aahnguye101024/LEDArtBoard/LEDBoard/LEDBoard/LEDBoard.sch

## KiCad design LEDBoard/LEDBoard/LEDBoard.sch (2024-01-31)

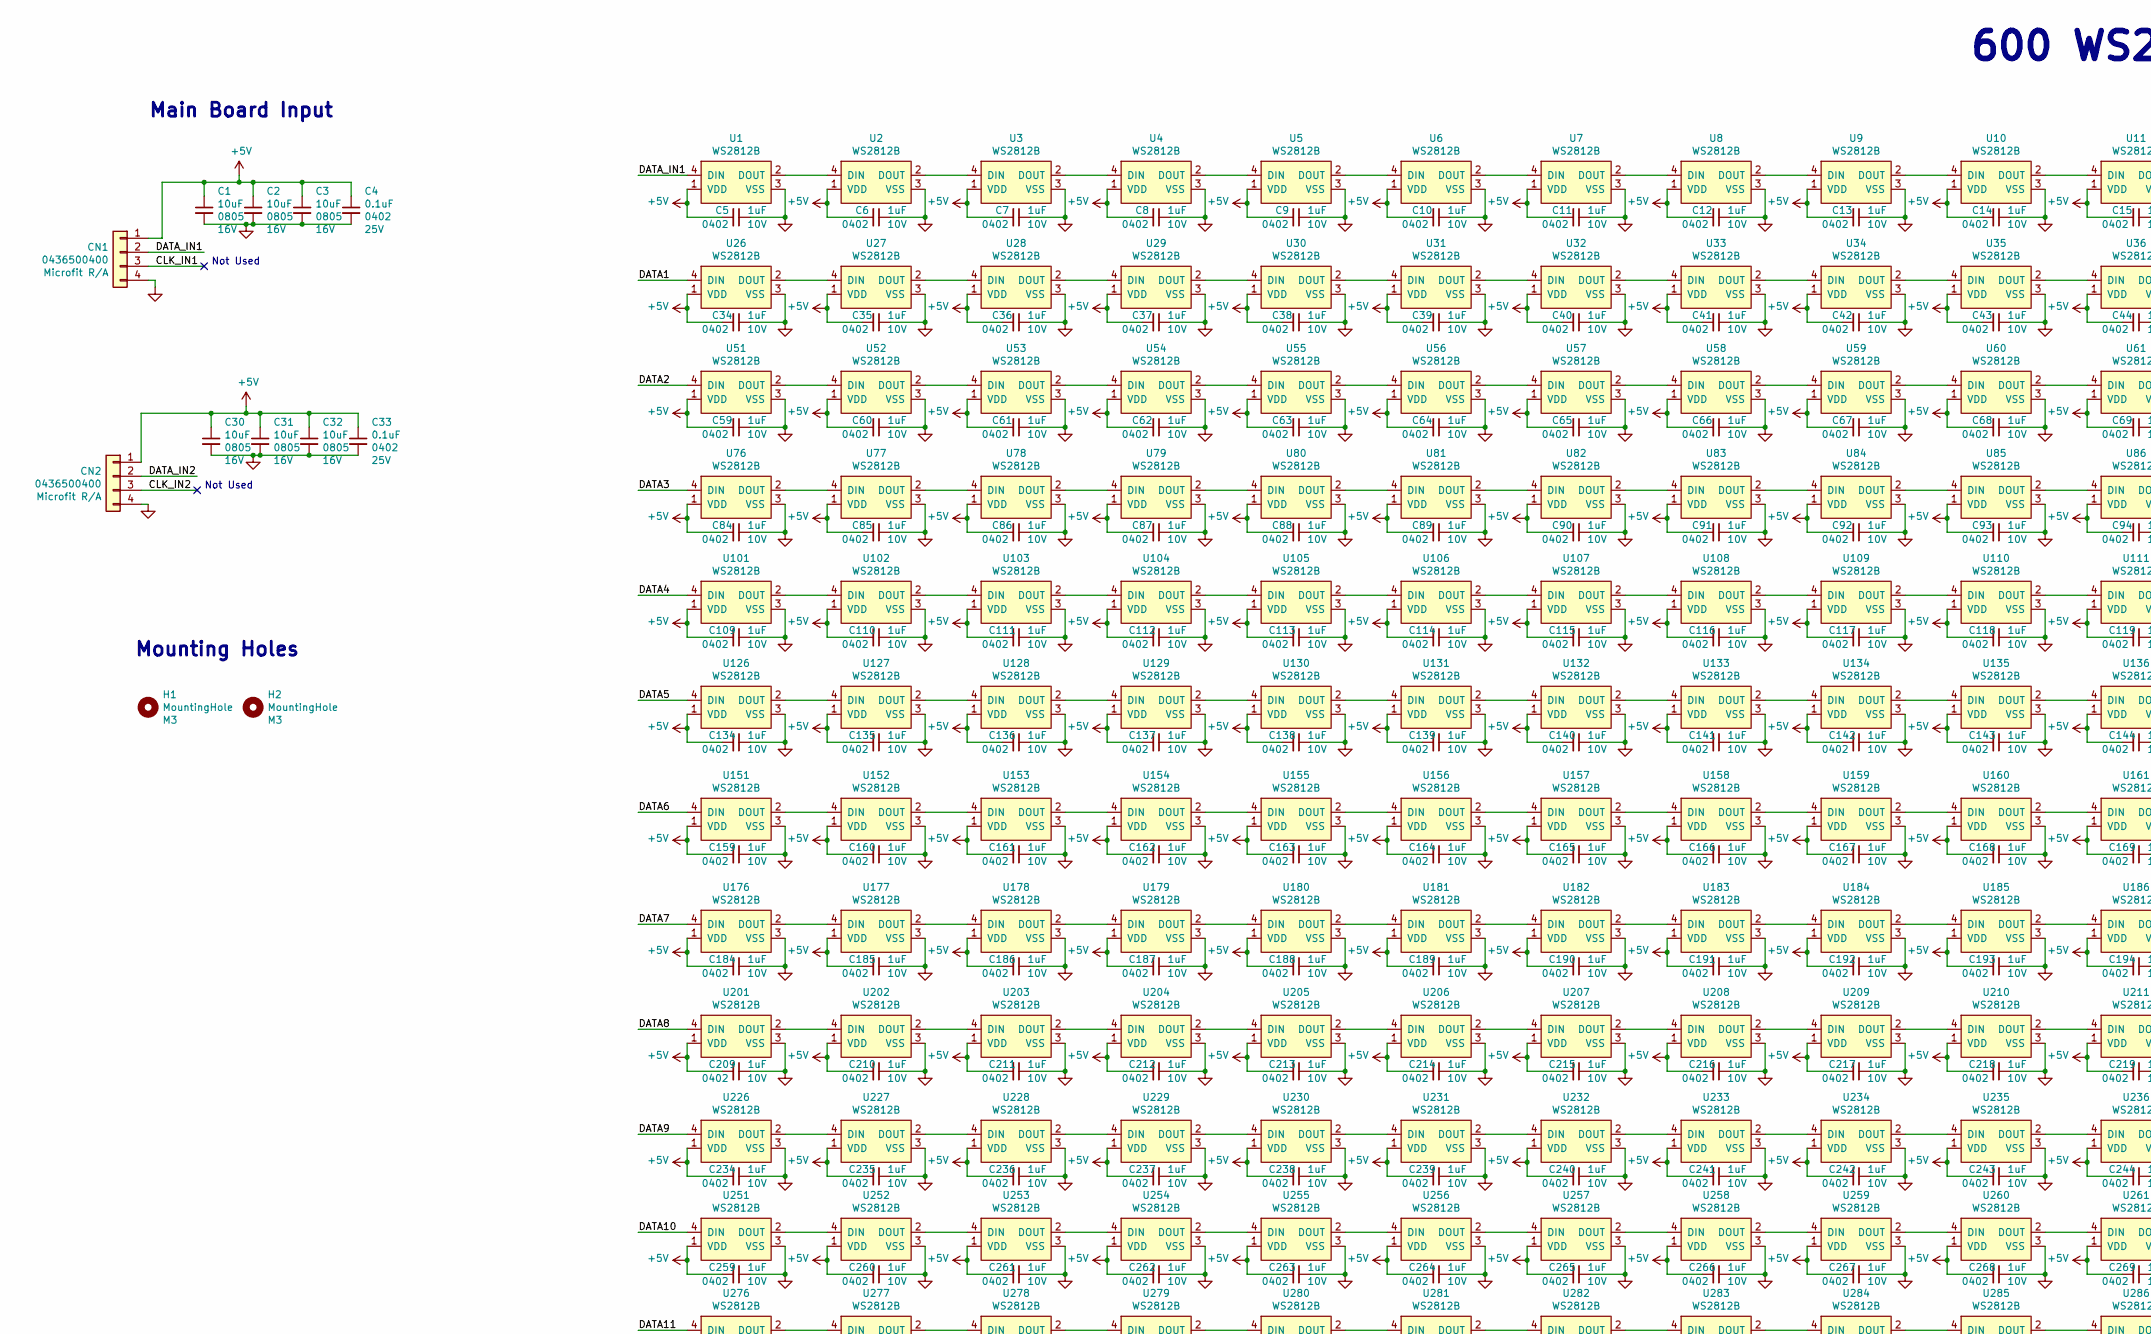
[picture p12: schematic LEDBoard.sch, part in row 1, column 1]

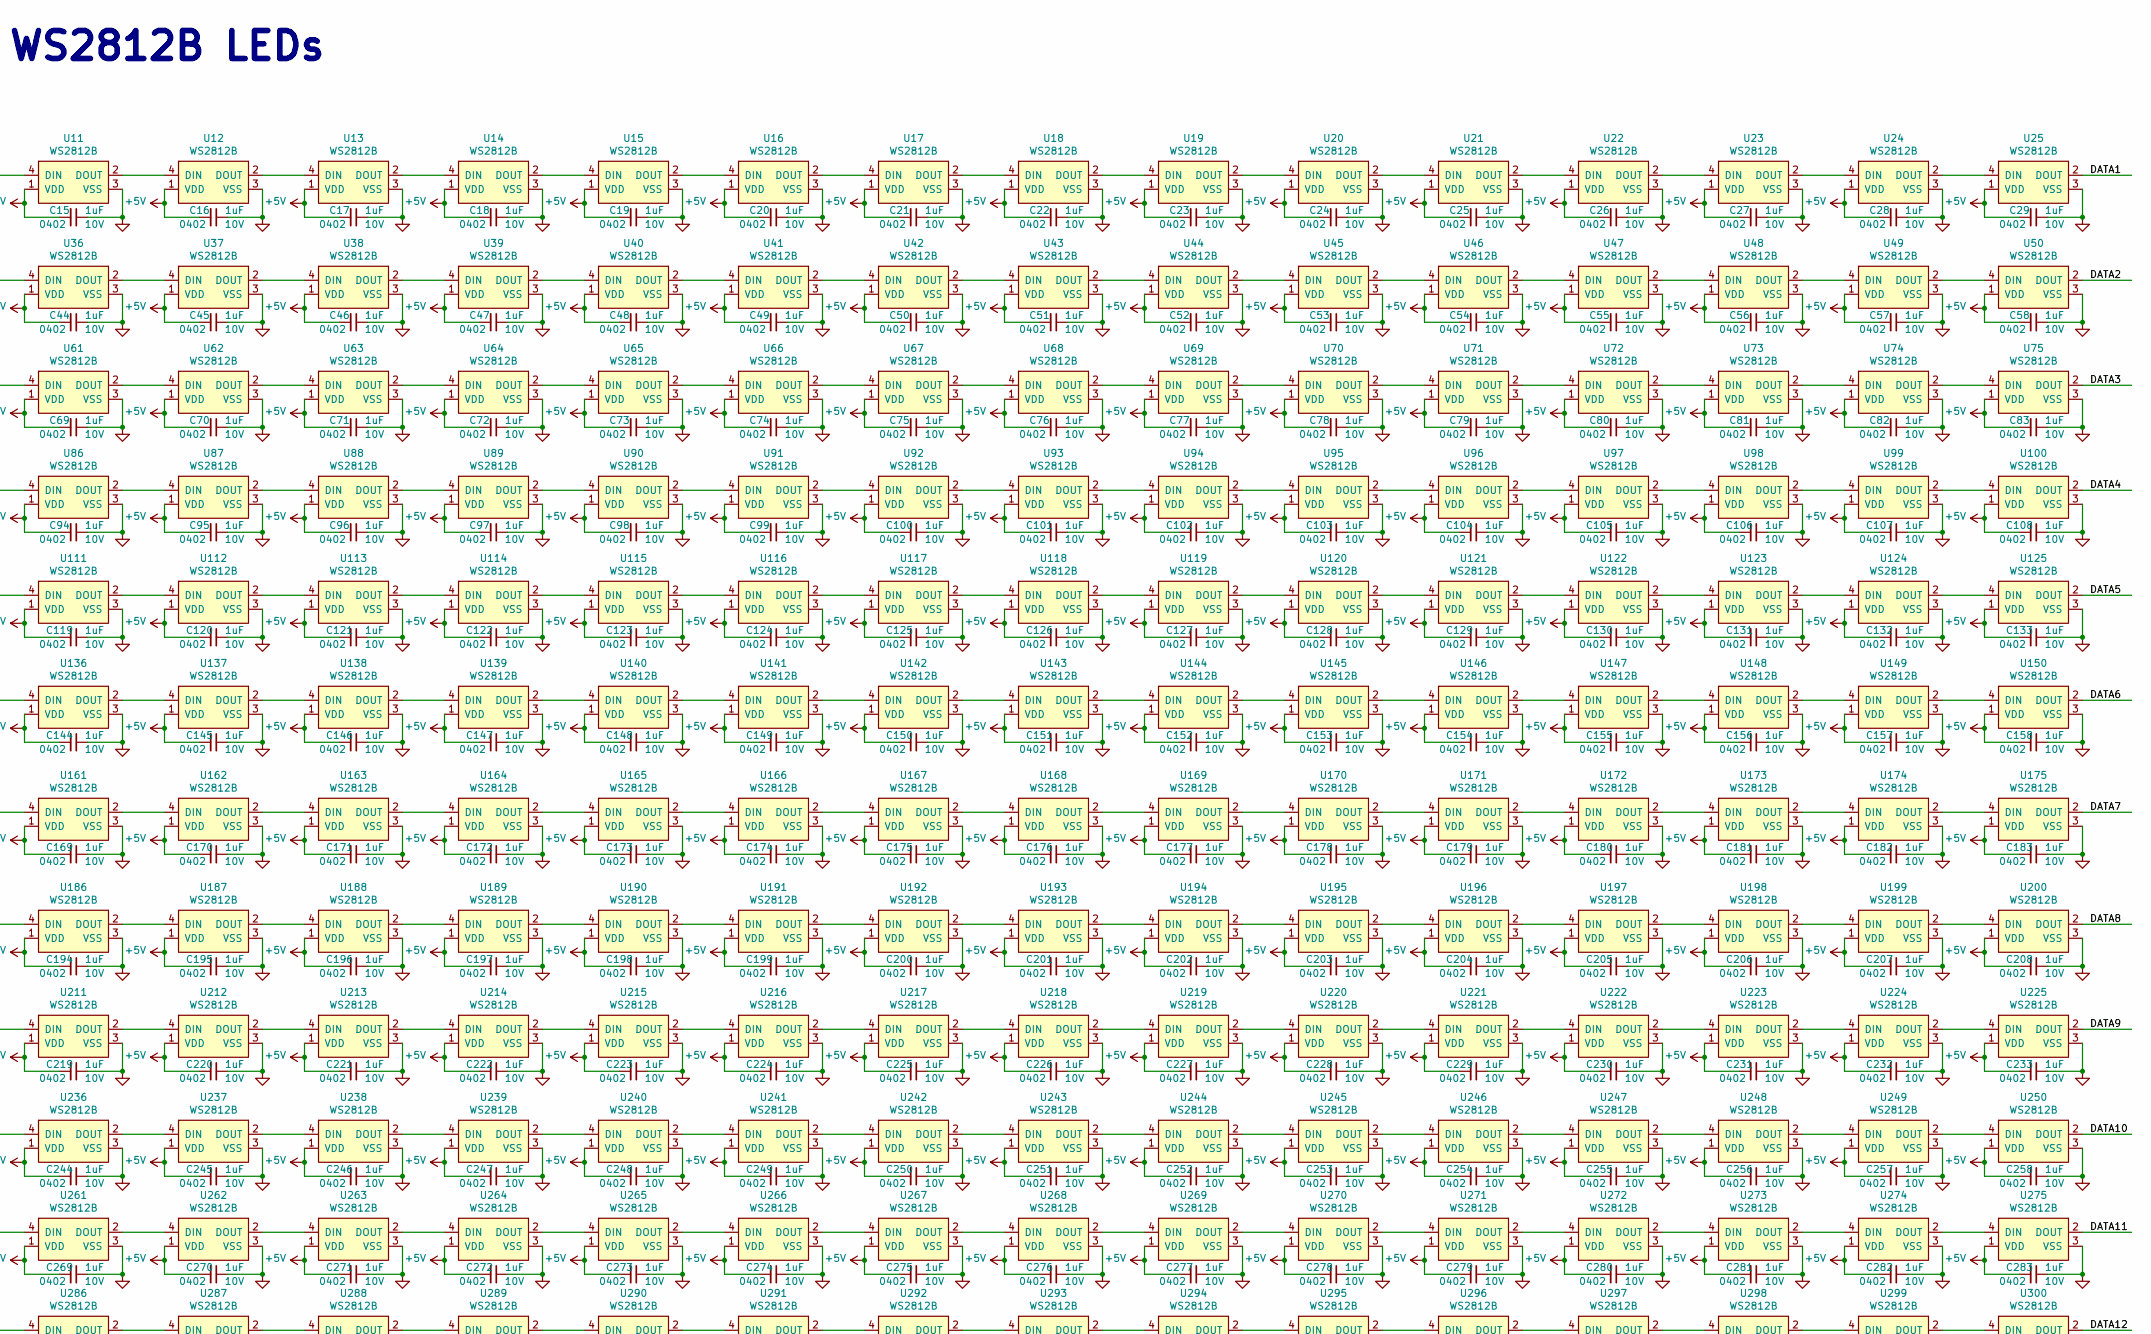
[picture p13: schematic LEDBoard.sch, part in row 1, column 2]

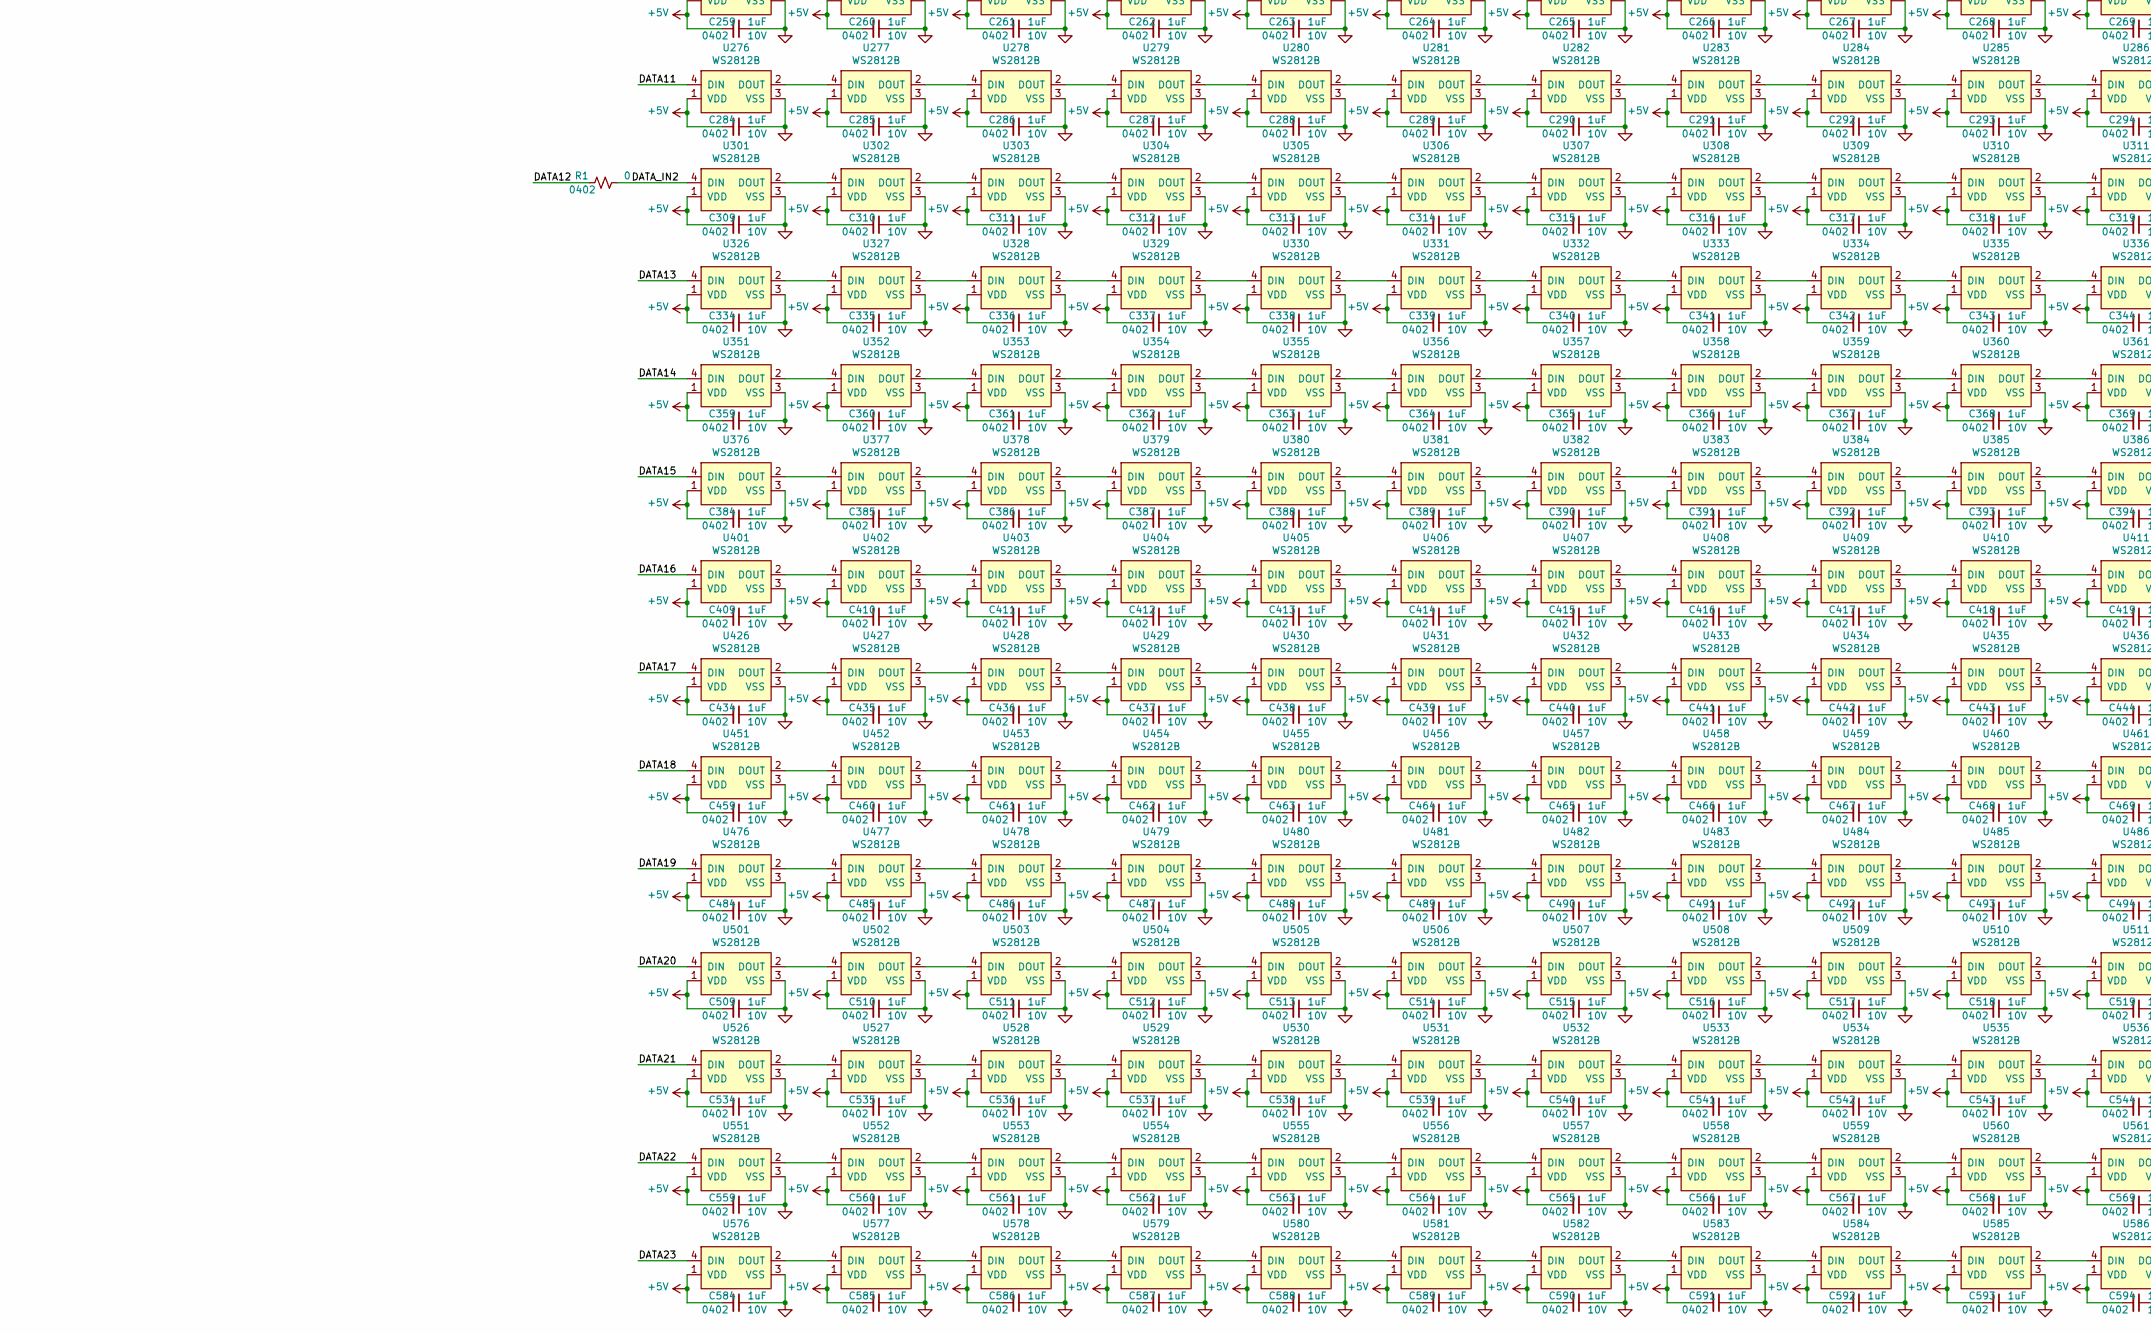
[picture p14: schematic LEDBoard.sch, part in row 2, column 1]

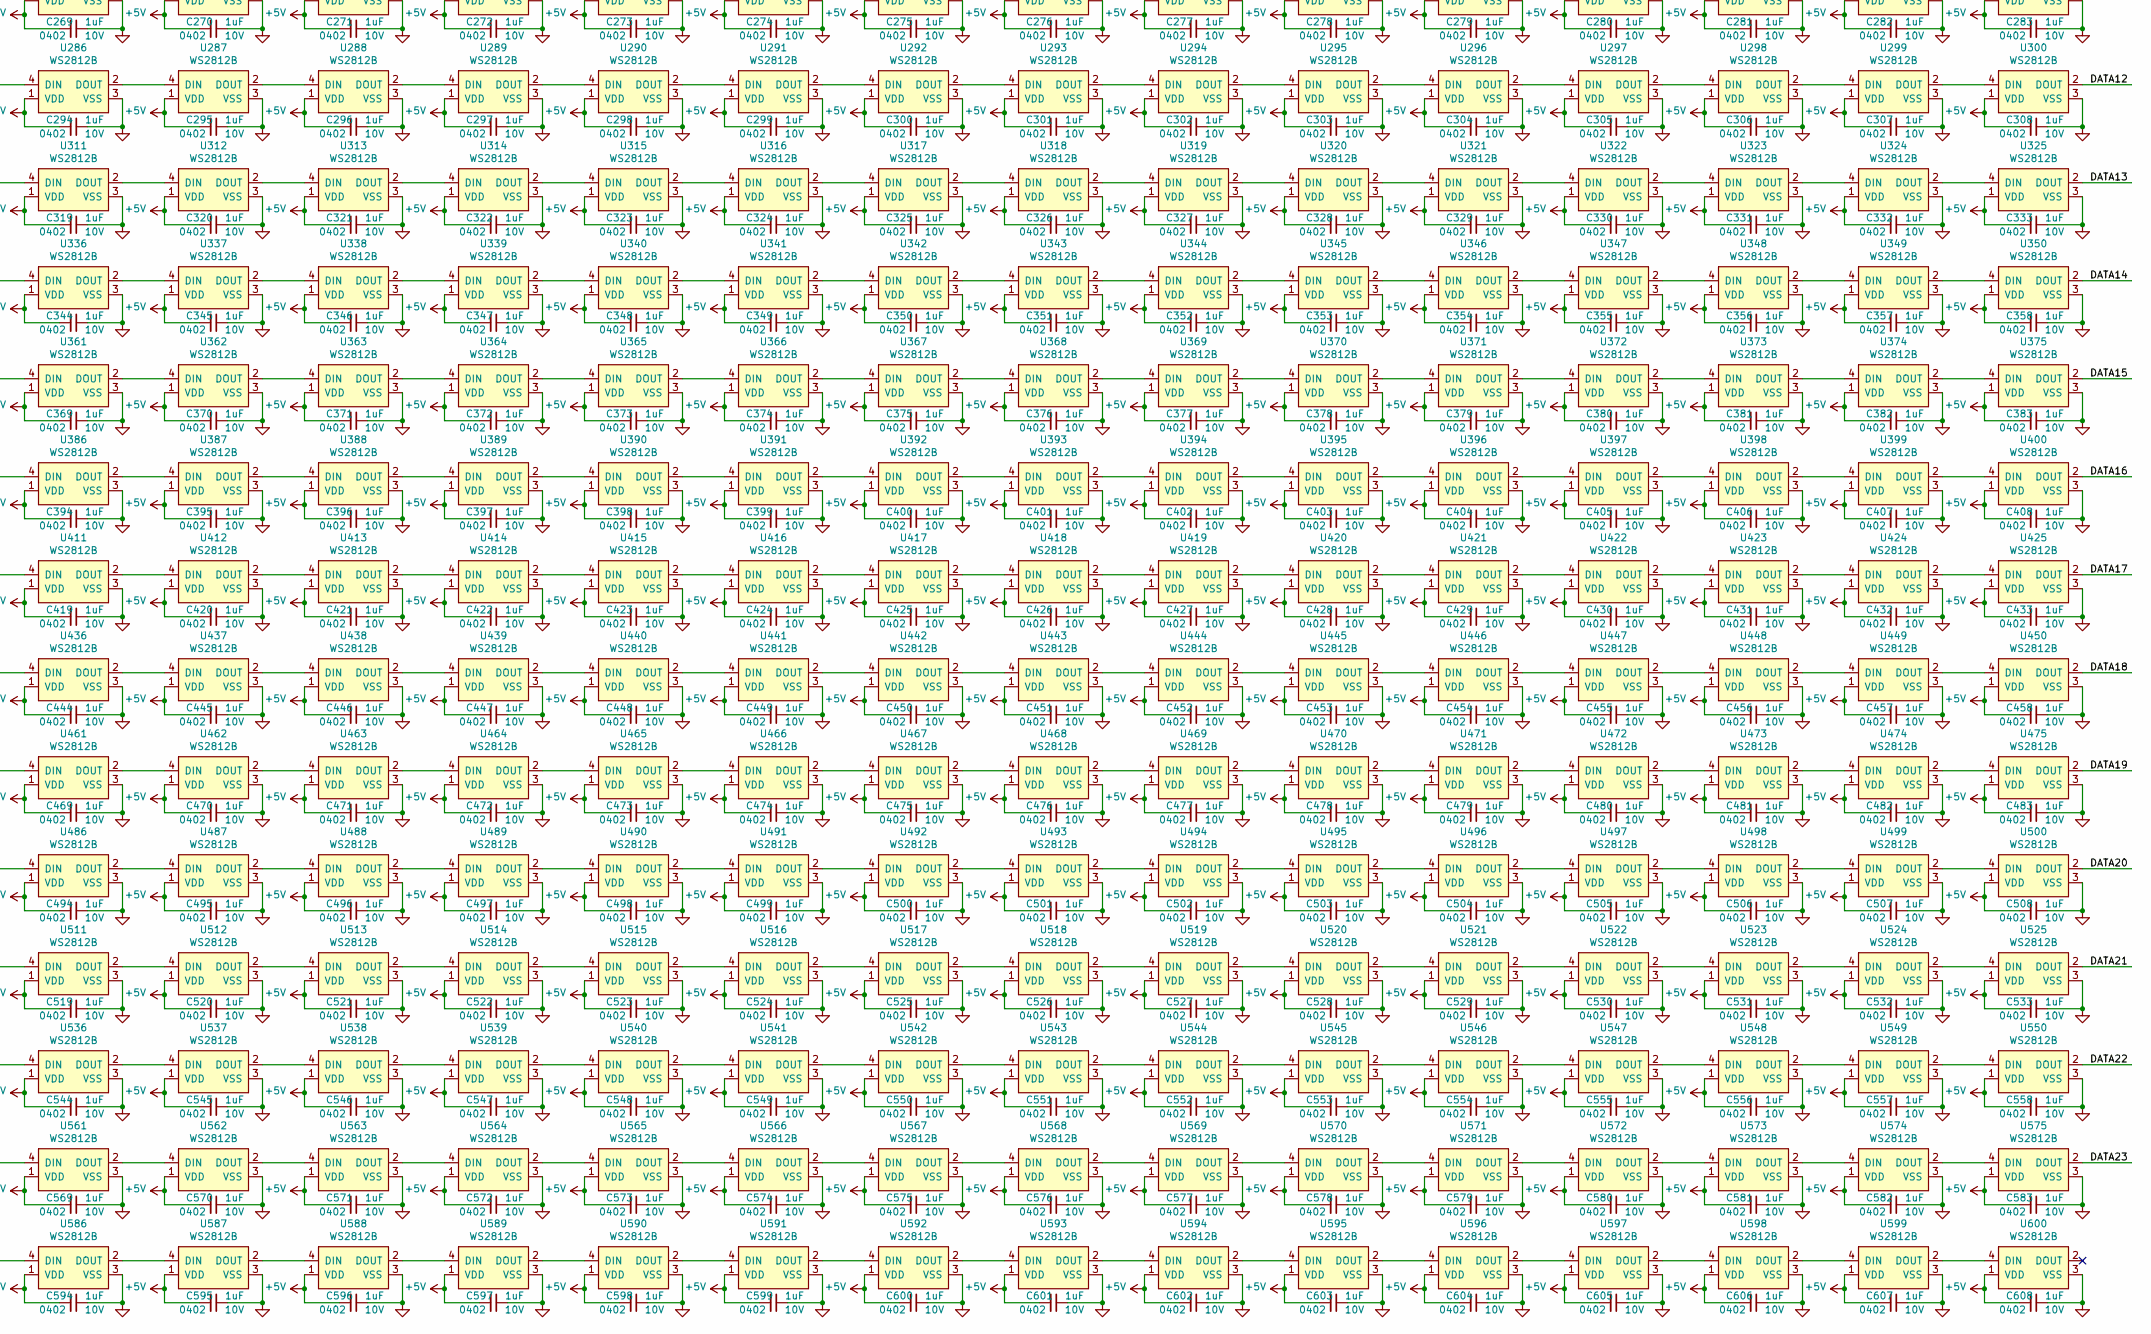
[picture p15: schematic LEDBoard.sch, part in row 2, column 2]

Parts:
C1, C2, C3, C30, C31, C32: 10uF; C_0805_2012Metric; Voltage 16V; Part Number 1276-2893-1-ND
C4, C33: 0.1uF; C_0402_1005Metric; Voltage 25V; Part Number 1276-1043-1-ND
C5, C6, C7, C8, C9, C10, C11, C12, C13, C14, C15, C16, C17, C18, C19, C20, C21, C22, C23, C24, C25, C26, C27, C28, C29, C34, C35, C36, C37, C38, C39, C40, C41, C42, C43, C44, C45, C46, C47, C48, C49, C50, C51, C52, C53, C54, C55, C56, C57, C58, C59, C60, C61, C62, C63, C64, C65, C66, C67, C68, C69, C70, C71, C72, C73, C74, C75, C76, C77, C78, C79, C80, C81, C82, C83, C84, C85, C86, C87, C88, C89, C90, C91, C92, C93, C94, C95, C96, C97, C98, C99, C100, C101, C102, C103, C104, C105, C106, C107, C108, C109, C110, C111, C112, C113, C114, C115, C116, C117, C118, C119, C120, C121, C122, C123, C124, C125, C126, C127, C128, C129, C130, C131, C132, C133, C134, C135, C136, C137, C138, C139, C140, C141, C142, C143, C144, C145, C146, C147, C148, C149, C150, C151, C152, C153, C154, C155, C156, C157, C158, C159, C160, C161, C162, C163, C164, C165, C166, C167, C168, C169, C170, C171, C172, C173, C174, C175, C176, C177, C178, C179, C180, C181, C182, C183, C184, C185, C186, C187, C188, C189, C190, C191, C192, C193, C194, C195, C196, C197, C198, C199, C200, C201, C202, C203, C204, C205, C206, C207, C208, C209, C210, C211, C212, C213, C214, C215, C216, C217, C218, C219, C220, C221, C222, C223, C224, C225, C226, C227, C228, C229, C230, C231, C232, C233, C234, C235, C236, C237, C238, C239, C240, C241, C242, C243, C244, C245, C246, C247, C248, C249, C250, C251, C252, C253, C254, C255, C256, C257, C258, C259, C260, C261, C262, C263, C264, C265, C266, C267, C268, C269, C270, C271, C272, C273, C274, C275, C276, C277, C278, C279, C280, C281, C282, C283, C284, C285, C286, C287, C288, C289, C290, C291, C292, C293, C294, C295, C296, C297, C298, C299, C300, C301, C302, C303, C304, C305, C306, C307, C308, C309, C310, C311, C312, C313, C314, C315, C316, C317, C318, C319, C320, C321, C322, C323, C324, C325, C326, C327, C328, C329, C330, C331, C332, C333, C334, C335, C336, C337, C338, C339, C340, C341, C342, C343, C344, C345, C346, C347, C348, C349, C350, C351, C352, C353, C354, C355, C356, C357, C358, C359, C360, C361, C362, C363, C364, C365, C366, C367, C368, C369, C370, C371, C372, C373, C374, C375, C376, C377, C378, C379, C380, C381, C382, C383, C384, C385, C386, C387, C388, C389, C390, C391, C392, C393, C394, C395, C396, C397, C398, C399, C400, C401, C402, C403, C404, C405, C406, C407, C408, C409, C410, C411, C412, C413, C414, C415, C416, C417, C418, C419, C420, C421, C422, C423, C424, C425, C426, C427, C428, C429, C430, C431, C432, C433, C434, C435, C436, C437, C438, C439, C440, C441, C442, C443, C444, C445, C446, C447, C448, C449, C450, C451, C452, C453, C454, C455, C456, C457, C458, C459, C460, C461, C462, C463, C464, C465, C466, C467, C468, C469, C470, C471, C472, C473, C474, C475, C476, C477, C478, C479, C480, C481, C482, C483, C484, C485, C486, C487, C488, C489, C490, C491, C492, C493, C494, C495, C496, C497, C498, C499, C500, C501, C502, C503, C504, C505, C506, C507, C508, C509, C510, C511, C512, C513, C514, C515, C516, C517, C518, C519, C520, C521, C522, C523, C524, C525, C526, C527, C528, C529, C530, C531, C532, C533, C534, C535, C536, C537, C538, C539, C540, C541, C542, C543, C544, C545, C546, C547, C548, C549, C550, C551, C552, C553, C554, C555, C556, C557, C558, C559, C560, C561, C562, C563, C564, C565, C566, C567, C568, C569, C570, C571, C572, C573, C574, C575, C576, C577, C578, C579, C580, C581, C582, C583, C584, C585, C586, C587, C588, C589, C590, C591, C592, C593, C594, C595, C596, C597, C598, C599, C600, C601, C602, C603, C604, C605, C606, C607, C608: 1uF; C_0402_1005Metric; Voltage 10V; Part Number 1276-1076-1-ND
CN1, CN2: 0436500400; MOLEX_43650-0400; Part Number WM1862-ND
H1, H2: MountingHole; MountingHole_3.2mm_M3_ISO7380
R1: 0; R_0402_1005Metric; Part Number RMCF0402ZT0R00CT-ND
U1, U2, U3, U4, U5, U6, U7, U8, U9, U10, U11, U12, U13, U14, U15, U16, U17, U18, U19, U20, U21, U22, U23, U24, U25, U26, U27, U28, U29, U30, U31, U32, U33, U34, U35, U36, U37, U38, U39, U40, U41, U42, U43, U44, U45, U46, U47, U48, U49, U50, U51, U52, U53, U54, U55, U56, U57, U58, U59, U60, U61, U62, U63, U64, U65, U66, U67, U68, U69, U70, U71, U72, U73, U74, U75, U76, U77, U78, U79, U80, U81, U82, U83, U84, U85, U86, U87, U88, U89, U90, U91, U92, U93, U94, U95, U96, U97, U98, U99, U100, U101, U102, U103, U104, U105, U106, U107, U108, U109, U110, U111, U112, U113, U114, U115, U116, U117, U118, U119, U120, U121, U122, U123, U124, U125, U126, U127, U128, U129, U130, U131, U132, U133, U134, U135, U136, U137, U138, U139, U140, U141, U142, U143, U144, U145, U146, U147, U148, U149, U150, U151, U152, U153, U154, U155, U156, U157, U158, U159, U160, U161, U162, U163, U164, U165, U166, U167, U168, U169, U170, U171, U172, U173, U174, U175, U176, U177, U178, U179, U180, U181, U182, U183, U184, U185, U186, U187, U188, U189, U190, U191, U192, U193, U194, U195, U196, U197, U198, U199, U200, U201, U202, U203, U204, U205, U206, U207, U208, U209, U210, U211, U212, U213, U214, U215, U216, U217, U218, U219, U220, U221, U222, U223, U224, U225, U226, U227, U228, U229, U230, U231, U232, U233, U234, U235, U236, U237, U238, U239, U240, U241, U242, U243, U244, U245, U246, U247, U248, U249, U250, U251, U252, U253, U254, U255, U256, U257, U258, U259, U260, U261, U262, U263, U264, U265, U266, U267, U268, U269, U270, U271, U272, U273, U274, U275, U276, U277, U278, U279, U280, U281, U282, U283, U284, U285, U286, U287, U288, U289, U290, U291, U292, U293, U294, U295, U296, U297, U298, U299, U300, U301, U302, U303, U304, U305, U306, U307, U308, U309, U310, U311, U312, U313, U314, U315, U316, U317, U318, U319, U320, U321, U322, U323, U324, U325, U326, U327, U328, U329, U330, U331, U332, U333, U334, U335, U336, U337, U338, U339, U340, U341, U342, U343, U344, U345, U346, U347, U348, U349, U350, U351, U352, U353, U354, U355, U356, U357, U358, U359, U360, U361, U362, U363, U364, U365, U366, U367, U368, U369, U370, U371, U372, U373, U374, U375, U376, U377, U378, U379, U380, U381, U382, U383, U384, U385, U386, U387, U388, U389, U390, U391, U392, U393, U394, U395, U396, U397, U398, U399, U400, U401, U402, U403, U404, U405, U406, U407, U408, U409, U410, U411, U412, U413, U414, U415, U416, U417, U418, U419, U420, U421, U422, U423, U424, U425, U426, U427, U428, U429, U430, U431, U432, U433, U434, U435, U436, U437, U438, U439, U440, U441, U442, U443, U444, U445, U446, U447, U448, U449, U450, U451, U452, U453, U454, U455, U456, U457, U458, U459, U460, U461, U462, U463, U464, U465, U466, U467, U468, U469, U470, U471, U472, U473, U474, U475, U476, U477, U478, U479, U480, U481, U482, U483, U484, U485, U486, U487, U488, U489, U490, U491, U492, U493, U494, U495, U496, U497, U498, U499, U500, U501, U502, U503, U504, U505, U506, U507, U508, U509, U510, U511, U512, U513, U514, U515, U516, U517, U518, U519, U520, U521, U522, U523, U524, U525, U526, U527, U528, U529, U530, U531, U532, U533, U534, U535, U536, U537, U538, U539, U540, U541, U542, U543, U544, U545, U546, U547, U548, U549, U550, U551, U552, U553, U554, U555, U556, U557, U558, U559, U560, U561, U562, U563, U564, U565, U566, U567, U568, U569, U570, U571, U572, U573, U574, U575, U576, U577, U578, U579, U580, U581, U582, U583, U584, U585, U586, U587, U588, U589, U590, U591, U592, U593, U594, U595, U596, U597, U598, U599, U600: WS2812B; LED_WS2812B-B; Part Number C2761795; JLCPCB Part Number C2761795

Connections:
+5V: C1.1, C2.1, C3.1, C4.1, C5.2, C6.2, C7.2, C8.2, C9.2, C10.2, C11.2, C12.2, C13.2, C14.2, C15.2, C16.2, C17.2, C18.2, C19.2, C20.2, C21.2, C22.2, C23.2, C24.2, C25.2, C26.2, C27.2, C28.2, C29.2, C30.1, C31.1, C32.1, C33.1, C34.2, C35.2, C36.2, C37.2, C38.2, C39.2, C40.2, C41.2, C42.2, C43.2, C44.2, C45.2, C46.2, C47.2, C48.2, C49.2, C50.2, C51.2, C52.2, C53.2, C54.2, C55.2, C56.2, C57.2, C58.2, C59.2, C60.2, C61.2, C62.2, C63.2, C64.2, C65.2, C66.2, C67.2, C68.2, C69.2, C70.2, C71.2, C72.2, C73.2, C74.2, C75.2, C76.2, C77.2, C78.2, C79.2, C80.2, C81.2, C82.2, C83.2, C84.2, C85.2, C86.2, C87.2, C88.2, C89.2, C90.2, C91.2, C92.2, C93.2, C94.2, C95.2, C96.2, C97.2, C98.2, C99.2, C100.2, C101.2, C102.2, C103.2, C104.2, C105.2, C106.2, C107.2, C108.2, C109.2, C110.2, C111.2, C112.2, C113.2, C114.2, C115.2, C116.2, C117.2, C118.2, C119.2, C120.2, C121.2, C122.2, C123.2, C124.2, C125.2, C126.2, C127.2, C128.2, C129.2, C130.2, C131.2, C132.2, C133.2, C134.2, C135.2, C136.2, C137.2, C138.2, C139.2, C140.2, C141.2, C142.2, C143.2, C144.2, C145.2, C146.2, C147.2, C148.2, C149.2, C150.2, C151.2, C152.2, C153.2, C154.2, C155.2, C156.2, C157.2, C158.2, C159.2, C160.2, C161.2, C162.2, C163.2, C164.2, C165.2, C166.2, C167.2, C168.2, C169.2, C170.2, C171.2, C172.2, C173.2, C174.2, C175.2, C176.2, C177.2, C178.2, C179.2, C180.2, C181.2, C182.2, C183.2, C184.2, C185.2, C186.2, C187.2, C188.2, C189.2, C190.2, C191.2, C192.2, C193.2, C194.2, C195.2, C196.2, C197.2, C198.2, C199.2, C200.2, C201.2, C202.2, C203.2, C204.2, C205.2, C206.2, C207.2, C208.2, C209.2, C210.2, C211.2, C212.2, C213.2, C214.2, C215.2, C216.2, C217.2, C218.2, C219.2, C220.2, C221.2, C222.2, C223.2, C224.2, C225.2, C226.2, C227.2, C228.2, C229.2, C230.2, C231.2, C232.2, C233.2, C234.2, C235.2, C236.2, C237.2, C238.2, C239.2, C240.2, C241.2, C242.2, C243.2, C244.2, C245.2, C246.2, C247.2, C248.2, C249.2, C250.2, C251.2, C252.2, C253.2, C254.2, C255.2, C256.2, C257.2, C258.2, C259.2, C260.2, C261.2, C262.2, C263.2, C264.2, C265.2, C266.2, C267.2, C268.2, C269.2, C270.2, C271.2, C272.2, C273.2, C274.2, C275.2, C276.2, C277.2, C278.2, C279.2, C280.2, C281.2, C282.2, C283.2, C284.2, C285.2, C286.2, C287.2, C288.2, C289.2, C290.2, C291.2, C292.2, C293.2, C294.2, C295.2, C296.2, C297.2, C298.2, C299.2, C300.2, C301.2, C302.2, C303.2, C304.2, C305.2, C306.2, C307.2, C308.2, C309.2, C310.2, C311.2, C312.2, C313.2, C314.2, C315.2, C316.2, C317.2, C318.2, C319.2, C320.2, C321.2, C322.2, C323.2, C324.2, C325.2, C326.2, C327.2, C328.2, C329.2, C330.2, C331.2, C332.2, C333.2, C334.2, C335.2, C336.2, C337.2, C338.2, C339.2, C340.2, C341.2, C342.2, C343.2, C344.2, C345.2, C346.2, C347.2, C348.2, C349.2, C350.2, C351.2, C352.2, C353.2, C354.2, C355.2, C356.2, C357.2, C358.2, C359.2, C360.2, C361.2, C362.2, C363.2, C364.2, C365.2, C366.2, C367.2, C368.2, C369.2, C370.2, C371.2, C372.2, C373.2, C374.2, C375.2, C376.2, C377.2, C378.2, C379.2, C380.2, C381.2, C382.2, C383.2, C384.2, C385.2, C386.2, C387.2, C388.2, C389.2, C390.2, C391.2, C392.2, C393.2, C394.2, C395.2, C396.2, C397.2, C398.2, C399.2, C400.2, C401.2, C402.2, C403.2, C404.2, C405.2, C406.2, C407.2, C408.2, C409.2, C410.2, C411.2, C412.2, C413.2, C414.2, C415.2, C416.2, C417.2, C418.2, C419.2, C420.2, C421.2, C422.2, C423.2, C424.2, C425.2, C426.2, C427.2, C428.2, C429.2, C430.2, C431.2, C432.2, C433.2, C434.2, C435.2, C436.2, C437.2, C438.2, C439.2, C440.2, C441.2, C442.2, C443.2, C444.2, C445.2, C446.2, C447.2, C448.2, C449.2, C450.2, C451.2, C452.2, C453.2, C454.2, C455.2, C456.2, C457.2, C458.2, C459.2, C460.2, C461.2, C462.2, C463.2, C464.2, C465.2, C466.2, C467.2, C468.2, C469.2, C470.2, C471.2, C472.2, C473.2, C474.2, C475.2, C476.2, C477.2, C478.2, C479.2, C480.2, C481.2, C482.2, C483.2, C484.2, C485.2, C486.2, C487.2, C488.2, C489.2, C490.2, C491.2, C492.2, C493.2, C494.2, C495.2, C496.2, C497.2, C498.2, C499.2, C500.2, C501.2, C502.2, C503.2, C504.2, C505.2, C506.2, C507.2, C508.2, C509.2, C510.2, C511.2, C512.2, C513.2, C514.2, C515.2, C516.2, C517.2, C518.2, C519.2, C520.2, C521.2, C522.2, C523.2, C524.2, C525.2, C526.2, C527.2, C528.2, C529.2, C530.2, C531.2, C532.2, C533.2, C534.2, C535.2, C536.2, C537.2, C538.2, C539.2, C540.2, C541.2, C542.2, C543.2, C544.2, C545.2, C546.2, C547.2, C548.2, C549.2, C550.2, C551.2, C552.2, C553.2, C554.2, C555.2, C556.2, C557.2, C558.2, C559.2, C560.2, C561.2, C562.2, C563.2, C564.2, C565.2, C566.2, C567.2, C568.2, C569.2, C570.2, C571.2, C572.2, C573.2, C574.2, C575.2, C576.2, C577.2, C578.2, C579.2, C580.2, C581.2, C582.2, C583.2, C584.2, C585.2, C586.2, C587.2, C588.2, C589.2, C590.2, C591.2, C592.2, C593.2, C594.2, C595.2, C596.2, C597.2, C598.2, C599.2, C600.2, C601.2, C602.2, C603.2, C604.2, C605.2, C606.2, C607.2, C608.2, CN1.1, CN2.1, U1.1 (VDD), U2.1 (VDD), U3.1 (VDD), U4.1 (VDD), U5.1 (VDD), U6.1 (VDD), U7.1 (VDD), U8.1 (VDD), U9.1 (VDD), U10.1 (VDD), U11.1 (VDD), U12.1 (VDD), U13.1 (VDD), U14.1 (VDD), U15.1 (VDD), U16.1 (VDD), U17.1 (VDD), U18.1 (VDD), U19.1 (VDD), U20.1 (VDD), U21.1 (VDD), U22.1 (VDD), U23.1 (VDD), U24.1 (VDD), U25.1 (VDD), U26.1 (VDD), U27.1 (VDD), U28.1 (VDD), U29.1 (VDD), U30.1 (VDD), U31.1 (VDD), U32.1 (VDD), U33.1 (VDD), U34.1 (VDD), U35.1 (VDD), U36.1 (VDD), U37.1 (VDD), U38.1 (VDD), U39.1 (VDD), U40.1 (VDD), U41.1 (VDD), U42.1 (VDD), U43.1 (VDD), U44.1 (VDD), U45.1 (VDD), U46.1 (VDD), U47.1 (VDD), U48.1 (VDD), U49.1 (VDD), U50.1 (VDD), U51.1 (VDD), U52.1 (VDD), U53.1 (VDD), U54.1 (VDD), U55.1 (VDD), U56.1 (VDD), U57.1 (VDD), U58.1 (VDD), U59.1 (VDD), U60.1 (VDD), U61.1 (VDD), U62.1 (VDD), U63.1 (VDD), U64.1 (VDD), U65.1 (VDD), U66.1 (VDD), U67.1 (VDD), U68.1 (VDD), U69.1 (VDD), U70.1 (VDD), U71.1 (VDD), U72.1 (VDD), U73.1 (VDD), U74.1 (VDD), U75.1 (VDD), U76.1 (VDD), U77.1 (VDD), U78.1 (VDD), U79.1 (VDD), U80.1 (VDD), U81.1 (VDD), U82.1 (VDD), U83.1 (VDD), U84.1 (VDD), U85.1 (VDD), U86.1 (VDD), U87.1 (VDD), U88.1 (VDD), U89.1 (VDD), U90.1 (VDD), U91.1 (VDD), U92.1 (VDD), U93.1 (VDD), U94.1 (VDD), U95.1 (VDD), U96.1 (VDD), U97.1 (VDD), U98.1 (VDD), U99.1 (VDD), U100.1 (VDD), U101.1 (VDD), U102.1 (VDD), U103.1 (VDD), U104.1 (VDD), U105.1 (VDD), U106.1 (VDD), U107.1 (VDD), U108.1 (VDD), U109.1 (VDD), U110.1 (VDD), U111.1 (VDD), U112.1 (VDD), U113.1 (VDD), U114.1 (VDD), U115.1 (VDD), U116.1 (VDD), U117.1 (VDD), U118.1 (VDD), U119.1 (VDD), U120.1 (VDD), U121.1 (VDD), U122.1 (VDD), U123.1 (VDD), U124.1 (VDD), U125.1 (VDD), U126.1 (VDD), U127.1 (VDD), U128.1 (VDD), U129.1 (VDD), U130.1 (VDD), U131.1 (VDD), U132.1 (VDD), U133.1 (VDD), U134.1 (VDD), U135.1 (VDD), U136.1 (VDD), U137.1 (VDD), U138.1 (VDD), U139.1 (VDD), U140.1 (VDD), U141.1 (VDD), U142.1 (VDD), U143.1 (VDD), U144.1 (VDD), U145.1 (VDD), U146.1 (VDD), U147.1 (VDD), U148.1 (VDD), U149.1 (VDD), U150.1 (VDD), U151.1 (VDD), U152.1 (VDD), U153.1 (VDD), U154.1 (VDD), U155.1 (VDD), U156.1 (VDD), U157.1 (VDD), U158.1 (VDD), U159.1 (VDD), U160.1 (VDD), U161.1 (VDD), U162.1 (VDD), U163.1 (VDD), U164.1 (VDD), U165.1 (VDD), U166.1 (VDD), U167.1 (VDD), U168.1 (VDD), U169.1 (VDD), U170.1 (VDD), U171.1 (VDD), U172.1 (VDD), U173.1 (VDD), U174.1 (VDD), U175.1 (VDD), U176.1 (VDD), U177.1 (VDD), U178.1 (VDD), U179.1 (VDD), U180.1 (VDD), U181.1 (VDD), U182.1 (VDD), U183.1 (VDD), U184.1 (VDD), U185.1 (VDD), U186.1 (VDD), U187.1 (VDD), U188.1 (VDD), U189.1 (VDD), U190.1 (VDD), U191.1 (VDD), U192.1 (VDD), U193.1 (VDD), U194.1 (VDD), U195.1 (VDD), U196.1 (VDD), U197.1 (VDD), U198.1 (VDD), U199.1 (VDD), U200.1 (VDD), U201.1 (VDD), U202.1 (VDD), U203.1 (VDD), U204.1 (VDD), U205.1 (VDD), U206.1 (VDD), U207.1 (VDD), U208.1 (VDD), U209.1 (VDD), U210.1 (VDD), U211.1 (VDD), U212.1 (VDD), U213.1 (VDD), U214.1 (VDD), U215.1 (VDD), U216.1 (VDD), U217.1 (VDD), U218.1 (VDD), U219.1 (VDD), U220.1 (VDD), U221.1 (VDD), U222.1 (VDD), U223.1 (VDD), U224.1 (VDD), U225.1 (VDD), U226.1 (VDD), U227.1 (VDD), U228.1 (VDD), U229.1 (VDD), U230.1 (VDD), U231.1 (VDD), U232.1 (VDD), U233.1 (VDD), U234.1 (VDD), U235.1 (VDD), U236.1 (VDD), U237.1 (VDD), U238.1 (VDD), U239.1 (VDD), U240.1 (VDD), U241.1 (VDD), U242.1 (VDD), U243.1 (VDD), U244.1 (VDD), U245.1 (VDD), U246.1 (VDD), U247.1 (VDD), U248.1 (VDD), U249.1 (VDD), U250.1 (VDD), U251.1 (VDD), U252.1 (VDD), U253.1 (VDD), U254.1 (VDD), U255.1 (VDD), U256.1 (VDD), U257.1 (VDD), U258.1 (VDD), U259.1 (VDD), U260.1 (VDD), U261.1 (VDD), U262.1 (VDD), U263.1 (VDD), U264.1 (VDD), U265.1 (VDD), U266.1 (VDD), U267.1 (VDD), U268.1 (VDD), U269.1 (VDD), U270.1 (VDD), U271.1 (VDD), U272.1 (VDD), U273.1 (VDD), U274.1 (VDD), U275.1 (VDD), U276.1 (VDD), U277.1 (VDD), U278.1 (VDD), U279.1 (VDD), U280.1 (VDD), U281.1 (VDD), U282.1 (VDD), U283.1 (VDD), U284.1 (VDD), U285.1 (VDD), U286.1 (VDD), U287.1 (VDD), U288.1 (VDD), U289.1 (VDD), U290.1 (VDD), U291.1 (VDD), U292.1 (VDD), U293.1 (VDD), U294.1 (VDD), U295.1 (VDD), U296.1 (VDD), U297.1 (VDD), U298.1 (VDD), U299.1 (VDD), U300.1 (VDD), U301.1 (VDD), U302.1 (VDD), U303.1 (VDD), U304.1 (VDD), U305.1 (VDD), U306.1 (VDD), U307.1 (VDD), U308.1 (VDD), U309.1 (VDD), U310.1 (VDD), U311.1 (VDD), U312.1 (VDD), U313.1 (VDD), U314.1 (VDD), U315.1 (VDD), U316.1 (VDD), U317.1 (VDD), U318.1 (VDD), U319.1 (VDD), U320.1 (VDD), U321.1 (VDD), U322.1 (VDD), U323.1 (VDD), U324.1 (VDD), U325.1 (VDD), U326.1 (VDD), U327.1 (VDD), U328.1 (VDD), U329.1 (VDD), U330.1 (VDD), U331.1 (VDD), U332.1 (VDD), U333.1 (VDD), U334.1 (VDD), U335.1 (VDD), U336.1 (VDD), U337.1 (VDD), U338.1 (VDD), U339.1 (VDD), U340.1 (VDD), U341.1 (VDD), U342.1 (VDD), U343.1 (VDD), U344.1 (VDD), U345.1 (VDD), U346.1 (VDD), U347.1 (VDD), U348.1 (VDD), U349.1 (VDD), U350.1 (VDD), U351.1 (VDD), U352.1 (VDD), U353.1 (VDD), U354.1 (VDD), U355.1 (VDD), U356.1 (VDD), U357.1 (VDD), U358.1 (VDD), U359.1 (VDD), U360.1 (VDD), U361.1 (VDD), U362.1 (VDD), U363.1 (VDD), U364.1 (VDD), U365.1 (VDD), U366.1 (VDD), U367.1 (VDD), U368.1 (VDD), U369.1 (VDD), U370.1 (VDD), U371.1 (VDD), U372.1 (VDD), U373.1 (VDD), U374.1 (VDD), U375.1 (VDD), U376.1 (VDD), U377.1 (VDD), U378.1 (VDD), U379.1 (VDD), U380.1 (VDD), U381.1 (VDD), U382.1 (VDD), U383.1 (VDD), U384.1 (VDD), U385.1 (VDD), U386.1 (VDD), U387.1 (VDD), U388.1 (VDD), U389.1 (VDD), U390.1 (VDD), U391.1 (VDD), U392.1 (VDD), U393.1 (VDD), U394.1 (VDD), U395.1 (VDD), U396.1 (VDD), U397.1 (VDD), U398.1 (VDD), U399.1 (VDD), U400.1 (VDD), U401.1 (VDD), U402.1 (VDD), U403.1 (VDD), U404.1 (VDD), U405.1 (VDD), U406.1 (VDD), U407.1 (VDD), U408.1 (VDD), U409.1 (VDD), U410.1 (VDD), U411.1 (VDD), U412.1 (VDD), U413.1 (VDD), U414.1 (VDD), U415.1 (VDD), U416.1 (VDD), U417.1 (VDD), U418.1 (VDD), U419.1 (VDD), U420.1 (VDD), U421.1 (VDD), U422.1 (VDD), U423.1 (VDD), U424.1 (VDD), U425.1 (VDD), U426.1 (VDD), U427.1 (VDD), U428.1 (VDD), U429.1 (VDD), U430.1 (VDD), U431.1 (VDD), U432.1 (VDD), U433.1 (VDD), U434.1 (VDD), U435.1 (VDD), U436.1 (VDD), U437.1 (VDD), U438.1 (VDD), U439.1 (VDD), U440.1 (VDD), U441.1 (VDD), U442.1 (VDD), U443.1 (VDD), U444.1 (VDD), U445.1 (VDD), U446.1 (VDD), U447.1 (VDD), U448.1 (VDD), U449.1 (VDD), U450.1 (VDD), U451.1 (VDD), U452.1 (VDD), U453.1 (VDD), U454.1 (VDD), U455.1 (VDD), U456.1 (VDD), U457.1 (VDD), U458.1 (VDD), U459.1 (VDD), U460.1 (VDD), U461.1 (VDD), U462.1 (VDD), U463.1 (VDD), U464.1 (VDD), U465.1 (VDD), U466.1 (VDD), U467.1 (VDD), U468.1 (VDD), U469.1 (VDD), U470.1 (VDD), U471.1 (VDD), U472.1 (VDD), U473.1 (VDD), U474.1 (VDD), U475.1 (VDD), U476.1 (VDD), U477.1 (VDD), U478.1 (VDD), U479.1 (VDD), U480.1 (VDD), U481.1 (VDD), U482.1 (VDD), U483.1 (VDD), U484.1 (VDD), U485.1 (VDD), U486.1 (VDD), U487.1 (VDD), U488.1 (VDD), U489.1 (VDD), U490.1 (VDD), U491.1 (VDD), U492.1 (VDD), U493.1 (VDD), U494.1 (VDD), U495.1 (VDD), U496.1 (VDD), U497.1 (VDD), U498.1 (VDD), U499.1 (VDD), U500.1 (VDD), U501.1 (VDD), U502.1 (VDD), U503.1 (VDD), U504.1 (VDD), U505.1 (VDD), U506.1 (VDD), U507.1 (VDD), U508.1 (VDD), U509.1 (VDD), U510.1 (VDD), U511.1 (VDD), U512.1 (VDD), U513.1 (VDD), U514.1 (VDD), U515.1 (VDD), U516.1 (VDD), U517.1 (VDD), U518.1 (VDD), U519.1 (VDD), U520.1 (VDD), U521.1 (VDD), U522.1 (VDD), U523.1 (VDD), U524.1 (VDD), U525.1 (VDD), U526.1 (VDD), U527.1 (VDD), U528.1 (VDD), U529.1 (VDD), U530.1 (VDD), U531.1 (VDD), U532.1 (VDD), U533.1 (VDD), U534.1 (VDD), U535.1 (VDD), U536.1 (VDD), U537.1 (VDD), U538.1 (VDD), U539.1 (VDD), U540.1 (VDD), U541.1 (VDD), U542.1 (VDD), U543.1 (VDD), U544.1 (VDD), U545.1 (VDD), U546.1 (VDD), U547.1 (VDD), U548.1 (VDD), U549.1 (VDD), U550.1 (VDD), U551.1 (VDD), U552.1 (VDD), U553.1 (VDD), U554.1 (VDD), U555.1 (VDD), U556.1 (VDD), U557.1 (VDD), U558.1 (VDD), U559.1 (VDD), U560.1 (VDD), U561.1 (VDD), U562.1 (VDD), U563.1 (VDD), U564.1 (VDD), U565.1 (VDD), U566.1 (VDD), U567.1 (VDD), U568.1 (VDD), U569.1 (VDD), U570.1 (VDD), U571.1 (VDD), U572.1 (VDD), U573.1 (VDD), U574.1 (VDD), U575.1 (VDD), U576.1 (VDD), U577.1 (VDD), U578.1 (VDD), U579.1 (VDD), U580.1 (VDD), U581.1 (VDD), U582.1 (VDD), U583.1 (VDD), U584.1 (VDD), U585.1 (VDD), U586.1 (VDD), U587.1 (VDD), U588.1 (VDD), U589.1 (VDD), U590.1 (VDD), U591.1 (VDD), U592.1 (VDD), U593.1 (VDD), U594.1 (VDD), U595.1 (VDD), U596.1 (VDD), U597.1 (VDD), U598.1 (VDD), U599.1 (VDD), U600.1 (VDD)
CLK_IN1: CN1.3
CLK_IN2: CN2.3
DATA1: U25.2 (DOUT), U26.4 (DIN)
DATA2: U50.2 (DOUT), U51.4 (DIN)
DATA3: U75.2 (DOUT), U76.4 (DIN)
DATA4: U100.2 (DOUT), U101.4 (DIN)
DATA5: U125.2 (DOUT), U126.4 (DIN)
DATA6: U150.2 (DOUT), U151.4 (DIN)
DATA7: U175.2 (DOUT), U176.4 (DIN)
DATA8: U200.2 (DOUT), U201.4 (DIN)
DATA9: U225.2 (DOUT), U226.4 (DIN)
DATA10: U250.2 (DOUT), U251.4 (DIN)
DATA11: U275.2 (DOUT), U276.4 (DIN)
DATA12: R1.1, U300.2 (DOUT)
DATA13: U325.2 (DOUT), U326.4 (DIN)
DATA14: U350.2 (DOUT), U351.4 (DIN)
DATA15: U375.2 (DOUT), U376.4 (DIN)
DATA16: U400.2 (DOUT), U401.4 (DIN)
DATA17: U425.2 (DOUT), U426.4 (DIN)
DATA18: U450.2 (DOUT), U451.4 (DIN)
DATA19: U475.2 (DOUT), U476.4 (DIN)
DATA20: U500.2 (DOUT), U501.4 (DIN)
DATA21: U525.2 (DOUT), U526.4 (DIN)
DATA22: U550.2 (DOUT), U551.4 (DIN)
DATA23: U575.2 (DOUT), U576.4 (DIN)
DATA_IN1: CN1.2, U1.4 (DIN)
DATA_IN2: CN2.2, R1.2, U301.4 (DIN)
GND: C1.2, C2.2, C3.2, C4.2, C5.1, C6.1, C7.1, C8.1, C9.1, C10.1, C11.1, C12.1, C13.1, C14.1, C15.1, C16.1, C17.1, C18.1, C19.1, C20.1, C21.1, C22.1, C23.1, C24.1, C25.1, C26.1, C27.1, C28.1, C29.1, C30.2, C31.2, C32.2, C33.2, C34.1, C35.1, C36.1, C37.1, C38.1, C39.1, C40.1, C41.1, C42.1, C43.1, C44.1, C45.1, C46.1, C47.1, C48.1, C49.1, C50.1, C51.1, C52.1, C53.1, C54.1, C55.1, C56.1, C57.1, C58.1, C59.1, C60.1, C61.1, C62.1, C63.1, C64.1, C65.1, C66.1, C67.1, C68.1, C69.1, C70.1, C71.1, C72.1, C73.1, C74.1, C75.1, C76.1, C77.1, C78.1, C79.1, C80.1, C81.1, C82.1, C83.1, C84.1, C85.1, C86.1, C87.1, C88.1, C89.1, C90.1, C91.1, C92.1, C93.1, C94.1, C95.1, C96.1, C97.1, C98.1, C99.1, C100.1, C101.1, C102.1, C103.1, C104.1, C105.1, C106.1, C107.1, C108.1, C109.1, C110.1, C111.1, C112.1, C113.1, C114.1, C115.1, C116.1, C117.1, C118.1, C119.1, C120.1, C121.1, C122.1, C123.1, C124.1, C125.1, C126.1, C127.1, C128.1, C129.1, C130.1, C131.1, C132.1, C133.1, C134.1, C135.1, C136.1, C137.1, C138.1, C139.1, C140.1, C141.1, C142.1, C143.1, C144.1, C145.1, C146.1, C147.1, C148.1, C149.1, C150.1, C151.1, C152.1, C153.1, C154.1, C155.1, C156.1, C157.1, C158.1, C159.1, C160.1, C161.1, C162.1, C163.1, C164.1, C165.1, C166.1, C167.1, C168.1, C169.1, C170.1, C171.1, C172.1, C173.1, C174.1, C175.1, C176.1, C177.1, C178.1, C179.1, C180.1, C181.1, C182.1, C183.1, C184.1, C185.1, C186.1, C187.1, C188.1, C189.1, C190.1, C191.1, C192.1, C193.1, C194.1, C195.1, C196.1, C197.1, C198.1, C199.1, C200.1, C201.1, C202.1, C203.1, C204.1, C205.1, C206.1, C207.1, C208.1, C209.1, C210.1, C211.1, C212.1, C213.1, C214.1, C215.1, C216.1, C217.1, C218.1, C219.1, C220.1, C221.1, C222.1, C223.1, C224.1, C225.1, C226.1, C227.1, C228.1, C229.1, C230.1, C231.1, C232.1, C233.1, C234.1, C235.1, C236.1, C237.1, C238.1, C239.1, C240.1, C241.1, C242.1, C243.1, C244.1, C245.1, C246.1, C247.1, C248.1, C249.1, C250.1, C251.1, C252.1, C253.1, C254.1, C255.1, C256.1, C257.1, C258.1, C259.1, C260.1, C261.1, C262.1, C263.1, C264.1, C265.1, C266.1, C267.1, C268.1, C269.1, C270.1, C271.1, C272.1, C273.1, C274.1, C275.1, C276.1, C277.1, C278.1, C279.1, C280.1, C281.1, C282.1, C283.1, C284.1, C285.1, C286.1, C287.1, C288.1, C289.1, C290.1, C291.1, C292.1, C293.1, C294.1, C295.1, C296.1, C297.1, C298.1, C299.1, C300.1, C301.1, C302.1, C303.1, C304.1, C305.1, C306.1, C307.1, C308.1, C309.1, C310.1, C311.1, C312.1, C313.1, C314.1, C315.1, C316.1, C317.1, C318.1, C319.1, C320.1, C321.1, C322.1, C323.1, C324.1, C325.1, C326.1, C327.1, C328.1, C329.1, C330.1, C331.1, C332.1, C333.1, C334.1, C335.1, C336.1, C337.1, C338.1, C339.1, C340.1, C341.1, C342.1, C343.1, C344.1, C345.1, C346.1, C347.1, C348.1, C349.1, C350.1, C351.1, C352.1, C353.1, C354.1, C355.1, C356.1, C357.1, C358.1, C359.1, C360.1, C361.1, C362.1, C363.1, C364.1, C365.1, C366.1, C367.1, C368.1, C369.1, C370.1, C371.1, C372.1, C373.1, C374.1, C375.1, C376.1, C377.1, C378.1, C379.1, C380.1, C381.1, C382.1, C383.1, C384.1, C385.1, C386.1, C387.1, C388.1, C389.1, C390.1, C391.1, C392.1, C393.1, C394.1, C395.1, C396.1, C397.1, C398.1, C399.1, C400.1, C401.1, C402.1, C403.1, C404.1, C405.1, C406.1, C407.1, C408.1, C409.1, C410.1, C411.1, C412.1, C413.1, C414.1, C415.1, C416.1, C417.1, C418.1, C419.1, C420.1, C421.1, C422.1, C423.1, C424.1, C425.1, C426.1, C427.1, C428.1, C429.1, C430.1, C431.1, C432.1, C433.1, C434.1, C435.1, C436.1, C437.1, C438.1, C439.1, C440.1, C441.1, C442.1, C443.1, C444.1, C445.1, C446.1, C447.1, C448.1, C449.1, C450.1, C451.1, C452.1, C453.1, C454.1, C455.1, C456.1, C457.1, C458.1, C459.1, C460.1, C461.1, C462.1, C463.1, C464.1, C465.1, C466.1, C467.1, C468.1, C469.1, C470.1, C471.1, C472.1, C473.1, C474.1, C475.1, C476.1, C477.1, C478.1, C479.1, C480.1, C481.1, C482.1, C483.1, C484.1, C485.1, C486.1, C487.1, C488.1, C489.1, C490.1, C491.1, C492.1, C493.1, C494.1, C495.1, C496.1, C497.1, C498.1, C499.1, C500.1, C501.1, C502.1, C503.1, C504.1, C505.1, C506.1, C507.1, C508.1, C509.1, C510.1, C511.1, C512.1, C513.1, C514.1, C515.1, C516.1, C517.1, C518.1, C519.1, C520.1, C521.1, C522.1, C523.1, C524.1, C525.1, C526.1, C527.1, C528.1, C529.1, C530.1, C531.1, C532.1, C533.1, C534.1, C535.1, C536.1, C537.1, C538.1, C539.1, C540.1, C541.1, C542.1, C543.1, C544.1, C545.1, C546.1, C547.1, C548.1, C549.1, C550.1, C551.1, C552.1, C553.1, C554.1, C555.1, C556.1, C557.1, C558.1, C559.1, C560.1, C561.1, C562.1, C563.1, C564.1, C565.1, C566.1, C567.1, C568.1, C569.1, C570.1, C571.1, C572.1, C573.1, C574.1, C575.1, C576.1, C577.1, C578.1, C579.1, C580.1, C581.1, C582.1, C583.1, C584.1, C585.1, C586.1, C587.1, C588.1, C589.1, C590.1, C591.1, C592.1, C593.1, C594.1, C595.1, C596.1, C597.1, C598.1, C599.1, C600.1, C601.1, C602.1, C603.1, C604.1, C605.1, C606.1, C607.1, C608.1, CN1.4, CN2.4, U1.3 (VSS), U2.3 (VSS), U3.3 (VSS), U4.3 (VSS), U5.3 (VSS), U6.3 (VSS), U7.3 (VSS), U8.3 (VSS), U9.3 (VSS), U10.3 (VSS), U11.3 (VSS), U12.3 (VSS), U13.3 (VSS), U14.3 (VSS), U15.3 (VSS), U16.3 (VSS), U17.3 (VSS), U18.3 (VSS), U19.3 (VSS), U20.3 (VSS), U21.3 (VSS), U22.3 (VSS), U23.3 (VSS), U24.3 (VSS), U25.3 (VSS), U26.3 (VSS), U27.3 (VSS), U28.3 (VSS), U29.3 (VSS), U30.3 (VSS), U31.3 (VSS), U32.3 (VSS), U33.3 (VSS), U34.3 (VSS), U35.3 (VSS), U36.3 (VSS), U37.3 (VSS), U38.3 (VSS), U39.3 (VSS), U40.3 (VSS), U41.3 (VSS), U42.3 (VSS), U43.3 (VSS), U44.3 (VSS), U45.3 (VSS), U46.3 (VSS), U47.3 (VSS), U48.3 (VSS), U49.3 (VSS), U50.3 (VSS), U51.3 (VSS), U52.3 (VSS), U53.3 (VSS), U54.3 (VSS), U55.3 (VSS), U56.3 (VSS), U57.3 (VSS), U58.3 (VSS), U59.3 (VSS), U60.3 (VSS), U61.3 (VSS), U62.3 (VSS), U63.3 (VSS), U64.3 (VSS), U65.3 (VSS), U66.3 (VSS), U67.3 (VSS), U68.3 (VSS), U69.3 (VSS), U70.3 (VSS), U71.3 (VSS), U72.3 (VSS), U73.3 (VSS), U74.3 (VSS), U75.3 (VSS), U76.3 (VSS), U77.3 (VSS), U78.3 (VSS), U79.3 (VSS), U80.3 (VSS), U81.3 (VSS), U82.3 (VSS), U83.3 (VSS), U84.3 (VSS), U85.3 (VSS), U86.3 (VSS), U87.3 (VSS), U88.3 (VSS), U89.3 (VSS), U90.3 (VSS), U91.3 (VSS), U92.3 (VSS), U93.3 (VSS), U94.3 (VSS), U95.3 (VSS), U96.3 (VSS), U97.3 (VSS), U98.3 (VSS), U99.3 (VSS), U100.3 (VSS), U101.3 (VSS), U102.3 (VSS), U103.3 (VSS), U104.3 (VSS), U105.3 (VSS), U106.3 (VSS), U107.3 (VSS), U108.3 (VSS), U109.3 (VSS), U110.3 (VSS), U111.3 (VSS), U112.3 (VSS), U113.3 (VSS), U114.3 (VSS), U115.3 (VSS), U116.3 (VSS), U117.3 (VSS), U118.3 (VSS), U119.3 (VSS), U120.3 (VSS), U121.3 (VSS), U122.3 (VSS), U123.3 (VSS), U124.3 (VSS), U125.3 (VSS), U126.3 (VSS), U127.3 (VSS), U128.3 (VSS), U129.3 (VSS), U130.3 (VSS), U131.3 (VSS), U132.3 (VSS), U133.3 (VSS), U134.3 (VSS), U135.3 (VSS), U136.3 (VSS), U137.3 (VSS), U138.3 (VSS), U139.3 (VSS), U140.3 (VSS), U141.3 (VSS), U142.3 (VSS), U143.3 (VSS), U144.3 (VSS), U145.3 (VSS), U146.3 (VSS), U147.3 (VSS), U148.3 (VSS), U149.3 (VSS), U150.3 (VSS), U151.3 (VSS), U152.3 (VSS), U153.3 (VSS), U154.3 (VSS), U155.3 (VSS), U156.3 (VSS), U157.3 (VSS), U158.3 (VSS), U159.3 (VSS), U160.3 (VSS), U161.3 (VSS), U162.3 (VSS), U163.3 (VSS), U164.3 (VSS), U165.3 (VSS), U166.3 (VSS), U167.3 (VSS), U168.3 (VSS), U169.3 (VSS), U170.3 (VSS), U171.3 (VSS), U172.3 (VSS), U173.3 (VSS), U174.3 (VSS), U175.3 (VSS), U176.3 (VSS), U177.3 (VSS), U178.3 (VSS), U179.3 (VSS), U180.3 (VSS), U181.3 (VSS), U182.3 (VSS), U183.3 (VSS), U184.3 (VSS), U185.3 (VSS), U186.3 (VSS), U187.3 (VSS), U188.3 (VSS), U189.3 (VSS), U190.3 (VSS), U191.3 (VSS), U192.3 (VSS), U193.3 (VSS), U194.3 (VSS), U195.3 (VSS), U196.3 (VSS), U197.3 (VSS), U198.3 (VSS), U199.3 (VSS), U200.3 (VSS), U201.3 (VSS), U202.3 (VSS), U203.3 (VSS), U204.3 (VSS), U205.3 (VSS), U206.3 (VSS), U207.3 (VSS), U208.3 (VSS), U209.3 (VSS), U210.3 (VSS), U211.3 (VSS), U212.3 (VSS), U213.3 (VSS), U214.3 (VSS), U215.3 (VSS), U216.3 (VSS), U217.3 (VSS), U218.3 (VSS), U219.3 (VSS), U220.3 (VSS), U221.3 (VSS), U222.3 (VSS), U223.3 (VSS), U224.3 (VSS), U225.3 (VSS), U226.3 (VSS), U227.3 (VSS), U228.3 (VSS), U229.3 (VSS), U230.3 (VSS), U231.3 (VSS), U232.3 (VSS), U233.3 (VSS), U234.3 (VSS), U235.3 (VSS), U236.3 (VSS), U237.3 (VSS), U238.3 (VSS), U239.3 (VSS), U240.3 (VSS), U241.3 (VSS), U242.3 (VSS), U243.3 (VSS), U244.3 (VSS), U245.3 (VSS), U246.3 (VSS), U247.3 (VSS), U248.3 (VSS), U249.3 (VSS), U250.3 (VSS), U251.3 (VSS), U252.3 (VSS), U253.3 (VSS), U254.3 (VSS), U255.3 (VSS), U256.3 (VSS), U257.3 (VSS), U258.3 (VSS), U259.3 (VSS), U260.3 (VSS), U261.3 (VSS), U262.3 (VSS), U263.3 (VSS), U264.3 (VSS), U265.3 (VSS), U266.3 (VSS), U267.3 (VSS), U268.3 (VSS), U269.3 (VSS), U270.3 (VSS), U271.3 (VSS), U272.3 (VSS), U273.3 (VSS), U274.3 (VSS), U275.3 (VSS), U276.3 (VSS), U277.3 (VSS), U278.3 (VSS), U279.3 (VSS), U280.3 (VSS), U281.3 (VSS), U282.3 (VSS), U283.3 (VSS), U284.3 (VSS), U285.3 (VSS), U286.3 (VSS), U287.3 (VSS), U288.3 (VSS), U289.3 (VSS), U290.3 (VSS), U291.3 (VSS), U292.3 (VSS), U293.3 (VSS), U294.3 (VSS), U295.3 (VSS), U296.3 (VSS), U297.3 (VSS), U298.3 (VSS), U299.3 (VSS), U300.3 (VSS), U301.3 (VSS), U302.3 (VSS), U303.3 (VSS), U304.3 (VSS), U305.3 (VSS), U306.3 (VSS), U307.3 (VSS), U308.3 (VSS), U309.3 (VSS), U310.3 (VSS), U311.3 (VSS), U312.3 (VSS), U313.3 (VSS), U314.3 (VSS), U315.3 (VSS), U316.3 (VSS), U317.3 (VSS), U318.3 (VSS), U319.3 (VSS), U320.3 (VSS), U321.3 (VSS), U322.3 (VSS), U323.3 (VSS), U324.3 (VSS), U325.3 (VSS), U326.3 (VSS), U327.3 (VSS), U328.3 (VSS), U329.3 (VSS), U330.3 (VSS), U331.3 (VSS), U332.3 (VSS), U333.3 (VSS), U334.3 (VSS), U335.3 (VSS), U336.3 (VSS), U337.3 (VSS), U338.3 (VSS), U339.3 (VSS), U340.3 (VSS), U341.3 (VSS), U342.3 (VSS), U343.3 (VSS), U344.3 (VSS), U345.3 (VSS), U346.3 (VSS), U347.3 (VSS), U348.3 (VSS), U349.3 (VSS), U350.3 (VSS), U351.3 (VSS), U352.3 (VSS), U353.3 (VSS), U354.3 (VSS), U355.3 (VSS), U356.3 (VSS), U357.3 (VSS), U358.3 (VSS), U359.3 (VSS), U360.3 (VSS), U361.3 (VSS), U362.3 (VSS), U363.3 (VSS), U364.3 (VSS), U365.3 (VSS), U366.3 (VSS), U367.3 (VSS), U368.3 (VSS), U369.3 (VSS), U370.3 (VSS), U371.3 (VSS), U372.3 (VSS), U373.3 (VSS), U374.3 (VSS), U375.3 (VSS), U376.3 (VSS), U377.3 (VSS), U378.3 (VSS), U379.3 (VSS), U380.3 (VSS), U381.3 (VSS), U382.3 (VSS), U383.3 (VSS), U384.3 (VSS), U385.3 (VSS), U386.3 (VSS), U387.3 (VSS), U388.3 (VSS), U389.3 (VSS), U390.3 (VSS), U391.3 (VSS), U392.3 (VSS), U393.3 (VSS), U394.3 (VSS), U395.3 (VSS), U396.3 (VSS), U397.3 (VSS), U398.3 (VSS), U399.3 (VSS), U400.3 (VSS), U401.3 (VSS), U402.3 (VSS), U403.3 (VSS), U404.3 (VSS), U405.3 (VSS), U406.3 (VSS), U407.3 (VSS), U408.3 (VSS), U409.3 (VSS), U410.3 (VSS), U411.3 (VSS), U412.3 (VSS), U413.3 (VSS), U414.3 (VSS), U415.3 (VSS), U416.3 (VSS), U417.3 (VSS), U418.3 (VSS), U419.3 (VSS), U420.3 (VSS), U421.3 (VSS), U422.3 (VSS), U423.3 (VSS), U424.3 (VSS), U425.3 (VSS), U426.3 (VSS), U427.3 (VSS), U428.3 (VSS), U429.3 (VSS), U430.3 (VSS), U431.3 (VSS), U432.3 (VSS), U433.3 (VSS), U434.3 (VSS), U435.3 (VSS), U436.3 (VSS), U437.3 (VSS), U438.3 (VSS), U439.3 (VSS), U440.3 (VSS), U441.3 (VSS), U442.3 (VSS), U443.3 (VSS), U444.3 (VSS), U445.3 (VSS), U446.3 (VSS), U447.3 (VSS), U448.3 (VSS), U449.3 (VSS), U450.3 (VSS), U451.3 (VSS), U452.3 (VSS), U453.3 (VSS), U454.3 (VSS), U455.3 (VSS), U456.3 (VSS), U457.3 (VSS), U458.3 (VSS), U459.3 (VSS), U460.3 (VSS), U461.3 (VSS), U462.3 (VSS), U463.3 (VSS), U464.3 (VSS), U465.3 (VSS), U466.3 (VSS), U467.3 (VSS), U468.3 (VSS), U469.3 (VSS), U470.3 (VSS), U471.3 (VSS), U472.3 (VSS), U473.3 (VSS), U474.3 (VSS), U475.3 (VSS), U476.3 (VSS), U477.3 (VSS), U478.3 (VSS), U479.3 (VSS), U480.3 (VSS), U481.3 (VSS), U482.3 (VSS), U483.3 (VSS), U484.3 (VSS), U485.3 (VSS), U486.3 (VSS), U487.3 (VSS), U488.3 (VSS), U489.3 (VSS), U490.3 (VSS), U491.3 (VSS), U492.3 (VSS), U493.3 (VSS), U494.3 (VSS), U495.3 (VSS), U496.3 (VSS), U497.3 (VSS), U498.3 (VSS), U499.3 (VSS), U500.3 (VSS), U501.3 (VSS), U502.3 (VSS), U503.3 (VSS), U504.3 (VSS), U505.3 (VSS), U506.3 (VSS), U507.3 (VSS), U508.3 (VSS), U509.3 (VSS), U510.3 (VSS), U511.3 (VSS), U512.3 (VSS), U513.3 (VSS), U514.3 (VSS), U515.3 (VSS), U516.3 (VSS), U517.3 (VSS), U518.3 (VSS), U519.3 (VSS), U520.3 (VSS), U521.3 (VSS), U522.3 (VSS), U523.3 (VSS), U524.3 (VSS), U525.3 (VSS), U526.3 (VSS), U527.3 (VSS), U528.3 (VSS), U529.3 (VSS), U530.3 (VSS), U531.3 (VSS), U532.3 (VSS), U533.3 (VSS), U534.3 (VSS), U535.3 (VSS), U536.3 (VSS), U537.3 (VSS), U538.3 (VSS), U539.3 (VSS), U540.3 (VSS), U541.3 (VSS), U542.3 (VSS), U543.3 (VSS), U544.3 (VSS), U545.3 (VSS), U546.3 (VSS), U547.3 (VSS), U548.3 (VSS), U549.3 (VSS), U550.3 (VSS), U551.3 (VSS), U552.3 (VSS), U553.3 (VSS), U554.3 (VSS), U555.3 (VSS), U556.3 (VSS), U557.3 (VSS), U558.3 (VSS), U559.3 (VSS), U560.3 (VSS), U561.3 (VSS), U562.3 (VSS), U563.3 (VSS), U564.3 (VSS), U565.3 (VSS), U566.3 (VSS), U567.3 (VSS), U568.3 (VSS), U569.3 (VSS), U570.3 (VSS), U571.3 (VSS), U572.3 (VSS), U573.3 (VSS), U574.3 (VSS), U575.3 (VSS), U576.3 (VSS), U577.3 (VSS), U578.3 (VSS), U579.3 (VSS), U580.3 (VSS), U581.3 (VSS), U582.3 (VSS), U583.3 (VSS), U584.3 (VSS), U585.3 (VSS), U586.3 (VSS), U587.3 (VSS), U588.3 (VSS), U589.3 (VSS), U590.3 (VSS), U591.3 (VSS), U592.3 (VSS), U593.3 (VSS), U594.3 (VSS), U595.3 (VSS), U596.3 (VSS), U597.3 (VSS), U598.3 (VSS), U599.3 (VSS), U600.3 (VSS)
unnamed: U1.2 (DOUT), U2.4 (DIN)
unnamed: U2.2 (DOUT), U3.4 (DIN)
unnamed: U3.2 (DOUT), U4.4 (DIN)
unnamed: U4.2 (DOUT), U5.4 (DIN)
unnamed: U5.2 (DOUT), U6.4 (DIN)
unnamed: U6.2 (DOUT), U7.4 (DIN)
unnamed: U7.2 (DOUT), U8.4 (DIN)
unnamed: U8.2 (DOUT), U9.4 (DIN)
unnamed: U10.2 (DOUT), U11.4 (DIN)
unnamed: U9.2 (DOUT), U10.4 (DIN)
unnamed: U11.2 (DOUT), U12.4 (DIN)
unnamed: U12.2 (DOUT), U13.4 (DIN)
unnamed: U13.2 (DOUT), U14.4 (DIN)
unnamed: U14.2 (DOUT), U15.4 (DIN)
unnamed: U15.2 (DOUT), U16.4 (DIN)
unnamed: U16.2 (DOUT), U17.4 (DIN)
unnamed: U17.2 (DOUT), U18.4 (DIN)
unnamed: U18.2 (DOUT), U19.4 (DIN)
unnamed: U19.2 (DOUT), U20.4 (DIN)
unnamed: U20.2 (DOUT), U21.4 (DIN)
unnamed: U21.2 (DOUT), U22.4 (DIN)
unnamed: U22.2 (DOUT), U23.4 (DIN)
unnamed: U23.2 (DOUT), U24.4 (DIN)
unnamed: U24.2 (DOUT), U25.4 (DIN)
unnamed: U26.2 (DOUT), U27.4 (DIN)
unnamed: U27.2 (DOUT), U28.4 (DIN)
unnamed: U28.2 (DOUT), U29.4 (DIN)
unnamed: U29.2 (DOUT), U30.4 (DIN)
unnamed: U30.2 (DOUT), U31.4 (DIN)
unnamed: U31.2 (DOUT), U32.4 (DIN)
unnamed: U32.2 (DOUT), U33.4 (DIN)
unnamed: U33.2 (DOUT), U34.4 (DIN)
unnamed: U34.2 (DOUT), U35.4 (DIN)
unnamed: U35.2 (DOUT), U36.4 (DIN)
unnamed: U36.2 (DOUT), U37.4 (DIN)
unnamed: U37.2 (DOUT), U38.4 (DIN)
unnamed: U38.2 (DOUT), U39.4 (DIN)
unnamed: U39.2 (DOUT), U40.4 (DIN)
unnamed: U40.2 (DOUT), U41.4 (DIN)
unnamed: U41.2 (DOUT), U42.4 (DIN)
unnamed: U42.2 (DOUT), U43.4 (DIN)
unnamed: U43.2 (DOUT), U44.4 (DIN)
unnamed: U44.2 (DOUT), U45.4 (DIN)
unnamed: U45.2 (DOUT), U46.4 (DIN)
unnamed: U46.2 (DOUT), U47.4 (DIN)
unnamed: U47.2 (DOUT), U48.4 (DIN)
unnamed: U48.2 (DOUT), U49.4 (DIN)
unnamed: U49.2 (DOUT), U50.4 (DIN)
unnamed: U51.2 (DOUT), U52.4 (DIN)
unnamed: U52.2 (DOUT), U53.4 (DIN)
unnamed: U53.2 (DOUT), U54.4 (DIN)
unnamed: U54.2 (DOUT), U55.4 (DIN)
unnamed: U55.2 (DOUT), U56.4 (DIN)
unnamed: U56.2 (DOUT), U57.4 (DIN)
unnamed: U57.2 (DOUT), U58.4 (DIN)
unnamed: U58.2 (DOUT), U59.4 (DIN)
unnamed: U59.2 (DOUT), U60.4 (DIN)
unnamed: U60.2 (DOUT), U61.4 (DIN)
unnamed: U61.2 (DOUT), U62.4 (DIN)
unnamed: U62.2 (DOUT), U63.4 (DIN)
unnamed: U63.2 (DOUT), U64.4 (DIN)
unnamed: U64.2 (DOUT), U65.4 (DIN)
unnamed: U65.2 (DOUT), U66.4 (DIN)
unnamed: U66.2 (DOUT), U67.4 (DIN)
unnamed: U67.2 (DOUT), U68.4 (DIN)
unnamed: U68.2 (DOUT), U69.4 (DIN)
unnamed: U69.2 (DOUT), U70.4 (DIN)
unnamed: U70.2 (DOUT), U71.4 (DIN)
unnamed: U71.2 (DOUT), U72.4 (DIN)
unnamed: U72.2 (DOUT), U73.4 (DIN)
unnamed: U73.2 (DOUT), U74.4 (DIN)
unnamed: U74.2 (DOUT), U75.4 (DIN)
unnamed: U76.2 (DOUT), U77.4 (DIN)
unnamed: U77.2 (DOUT), U78.4 (DIN)
unnamed: U78.2 (DOUT), U79.4 (DIN)
unnamed: U79.2 (DOUT), U80.4 (DIN)
unnamed: U80.2 (DOUT), U81.4 (DIN)
unnamed: U81.2 (DOUT), U82.4 (DIN)
unnamed: U82.2 (DOUT), U83.4 (DIN)
unnamed: U83.2 (DOUT), U84.4 (DIN)
unnamed: U84.2 (DOUT), U85.4 (DIN)
unnamed: U85.2 (DOUT), U86.4 (DIN)
unnamed: U86.2 (DOUT), U87.4 (DIN)
unnamed: U87.2 (DOUT), U88.4 (DIN)
unnamed: U88.2 (DOUT), U89.4 (DIN)
unnamed: U89.2 (DOUT), U90.4 (DIN)
unnamed: U90.2 (DOUT), U91.4 (DIN)
unnamed: U91.2 (DOUT), U92.4 (DIN)
unnamed: U92.2 (DOUT), U93.4 (DIN)
unnamed: U93.2 (DOUT), U94.4 (DIN)
unnamed: U94.2 (DOUT), U95.4 (DIN)
unnamed: U95.2 (DOUT), U96.4 (DIN)
unnamed: U96.2 (DOUT), U97.4 (DIN)
unnamed: U97.2 (DOUT), U98.4 (DIN)
unnamed: U98.2 (DOUT), U99.4 (DIN)
unnamed: U99.2 (DOUT), U100.4 (DIN)
unnamed: U101.2 (DOUT), U102.4 (DIN)
unnamed: U102.2 (DOUT), U103.4 (DIN)
unnamed: U103.2 (DOUT), U104.4 (DIN)
unnamed: U104.2 (DOUT), U105.4 (DIN)
unnamed: U105.2 (DOUT), U106.4 (DIN)
unnamed: U106.2 (DOUT), U107.4 (DIN)
unnamed: U107.2 (DOUT), U108.4 (DIN)
unnamed: U108.2 (DOUT), U109.4 (DIN)
unnamed: U109.2 (DOUT), U110.4 (DIN)
unnamed: U110.2 (DOUT), U111.4 (DIN)
unnamed: U111.2 (DOUT), U112.4 (DIN)
unnamed: U112.2 (DOUT), U113.4 (DIN)
unnamed: U113.2 (DOUT), U114.4 (DIN)
unnamed: U114.2 (DOUT), U115.4 (DIN)
unnamed: U115.2 (DOUT), U116.4 (DIN)
unnamed: U116.2 (DOUT), U117.4 (DIN)
unnamed: U117.2 (DOUT), U118.4 (DIN)
unnamed: U118.2 (DOUT), U119.4 (DIN)
unnamed: U119.2 (DOUT), U120.4 (DIN)
unnamed: U120.2 (DOUT), U121.4 (DIN)
unnamed: U121.2 (DOUT), U122.4 (DIN)
unnamed: U122.2 (DOUT), U123.4 (DIN)
unnamed: U123.2 (DOUT), U124.4 (DIN)
unnamed: U124.2 (DOUT), U125.4 (DIN)
unnamed: U126.2 (DOUT), U127.4 (DIN)
unnamed: U127.2 (DOUT), U128.4 (DIN)
unnamed: U128.2 (DOUT), U129.4 (DIN)
unnamed: U129.2 (DOUT), U130.4 (DIN)
unnamed: U130.2 (DOUT), U131.4 (DIN)
unnamed: U131.2 (DOUT), U132.4 (DIN)
unnamed: U132.2 (DOUT), U133.4 (DIN)
unnamed: U133.2 (DOUT), U134.4 (DIN)
unnamed: U134.2 (DOUT), U135.4 (DIN)
unnamed: U135.2 (DOUT), U136.4 (DIN)
unnamed: U136.2 (DOUT), U137.4 (DIN)
unnamed: U137.2 (DOUT), U138.4 (DIN)
unnamed: U138.2 (DOUT), U139.4 (DIN)
unnamed: U139.2 (DOUT), U140.4 (DIN)
unnamed: U140.2 (DOUT), U141.4 (DIN)
unnamed: U141.2 (DOUT), U142.4 (DIN)
unnamed: U142.2 (DOUT), U143.4 (DIN)
unnamed: U143.2 (DOUT), U144.4 (DIN)
unnamed: U144.2 (DOUT), U145.4 (DIN)
unnamed: U145.2 (DOUT), U146.4 (DIN)
unnamed: U146.2 (DOUT), U147.4 (DIN)
unnamed: U147.2 (DOUT), U148.4 (DIN)
unnamed: U148.2 (DOUT), U149.4 (DIN)
unnamed: U149.2 (DOUT), U150.4 (DIN)
unnamed: U151.2 (DOUT), U152.4 (DIN)
unnamed: U152.2 (DOUT), U153.4 (DIN)
unnamed: U153.2 (DOUT), U154.4 (DIN)
unnamed: U154.2 (DOUT), U155.4 (DIN)
unnamed: U155.2 (DOUT), U156.4 (DIN)
unnamed: U156.2 (DOUT), U157.4 (DIN)
unnamed: U157.2 (DOUT), U158.4 (DIN)
unnamed: U158.2 (DOUT), U159.4 (DIN)
unnamed: U159.2 (DOUT), U160.4 (DIN)
unnamed: U160.2 (DOUT), U161.4 (DIN)
unnamed: U161.2 (DOUT), U162.4 (DIN)
unnamed: U162.2 (DOUT), U163.4 (DIN)
unnamed: U163.2 (DOUT), U164.4 (DIN)
unnamed: U164.2 (DOUT), U165.4 (DIN)
unnamed: U165.2 (DOUT), U166.4 (DIN)
unnamed: U166.2 (DOUT), U167.4 (DIN)
unnamed: U167.2 (DOUT), U168.4 (DIN)
unnamed: U168.2 (DOUT), U169.4 (DIN)
unnamed: U169.2 (DOUT), U170.4 (DIN)
unnamed: U170.2 (DOUT), U171.4 (DIN)
unnamed: U171.2 (DOUT), U172.4 (DIN)
unnamed: U172.2 (DOUT), U173.4 (DIN)
unnamed: U173.2 (DOUT), U174.4 (DIN)
unnamed: U174.2 (DOUT), U175.4 (DIN)
unnamed: U176.2 (DOUT), U177.4 (DIN)
unnamed: U177.2 (DOUT), U178.4 (DIN)
unnamed: U178.2 (DOUT), U179.4 (DIN)
unnamed: U179.2 (DOUT), U180.4 (DIN)
unnamed: U180.2 (DOUT), U181.4 (DIN)
unnamed: U181.2 (DOUT), U182.4 (DIN)
unnamed: U182.2 (DOUT), U183.4 (DIN)
unnamed: U183.2 (DOUT), U184.4 (DIN)
unnamed: U184.2 (DOUT), U185.4 (DIN)
unnamed: U185.2 (DOUT), U186.4 (DIN)
unnamed: U186.2 (DOUT), U187.4 (DIN)
unnamed: U187.2 (DOUT), U188.4 (DIN)
unnamed: U188.2 (DOUT), U189.4 (DIN)
unnamed: U189.2 (DOUT), U190.4 (DIN)
unnamed: U190.2 (DOUT), U191.4 (DIN)
unnamed: U191.2 (DOUT), U192.4 (DIN)
unnamed: U192.2 (DOUT), U193.4 (DIN)
unnamed: U193.2 (DOUT), U194.4 (DIN)
unnamed: U194.2 (DOUT), U195.4 (DIN)
unnamed: U195.2 (DOUT), U196.4 (DIN)
unnamed: U196.2 (DOUT), U197.4 (DIN)
unnamed: U197.2 (DOUT), U198.4 (DIN)
unnamed: U198.2 (DOUT), U199.4 (DIN)
unnamed: U199.2 (DOUT), U200.4 (DIN)
unnamed: U201.2 (DOUT), U202.4 (DIN)
unnamed: U202.2 (DOUT), U203.4 (DIN)
unnamed: U203.2 (DOUT), U204.4 (DIN)
unnamed: U204.2 (DOUT), U205.4 (DIN)
unnamed: U205.2 (DOUT), U206.4 (DIN)
unnamed: U206.2 (DOUT), U207.4 (DIN)
unnamed: U207.2 (DOUT), U208.4 (DIN)
unnamed: U208.2 (DOUT), U209.4 (DIN)
unnamed: U209.2 (DOUT), U210.4 (DIN)
unnamed: U210.2 (DOUT), U211.4 (DIN)
unnamed: U211.2 (DOUT), U212.4 (DIN)
unnamed: U212.2 (DOUT), U213.4 (DIN)
unnamed: U213.2 (DOUT), U214.4 (DIN)
unnamed: U214.2 (DOUT), U215.4 (DIN)
unnamed: U215.2 (DOUT), U216.4 (DIN)
unnamed: U216.2 (DOUT), U217.4 (DIN)
unnamed: U217.2 (DOUT), U218.4 (DIN)
unnamed: U218.2 (DOUT), U219.4 (DIN)
unnamed: U219.2 (DOUT), U220.4 (DIN)
unnamed: U220.2 (DOUT), U221.4 (DIN)
unnamed: U221.2 (DOUT), U222.4 (DIN)
unnamed: U222.2 (DOUT), U223.4 (DIN)
unnamed: U223.2 (DOUT), U224.4 (DIN)
unnamed: U224.2 (DOUT), U225.4 (DIN)
unnamed: U226.2 (DOUT), U227.4 (DIN)
unnamed: U227.2 (DOUT), U228.4 (DIN)
unnamed: U228.2 (DOUT), U229.4 (DIN)
unnamed: U229.2 (DOUT), U230.4 (DIN)
unnamed: U230.2 (DOUT), U231.4 (DIN)
unnamed: U231.2 (DOUT), U232.4 (DIN)
unnamed: U232.2 (DOUT), U233.4 (DIN)
unnamed: U233.2 (DOUT), U234.4 (DIN)
unnamed: U234.2 (DOUT), U235.4 (DIN)
unnamed: U235.2 (DOUT), U236.4 (DIN)
unnamed: U236.2 (DOUT), U237.4 (DIN)
unnamed: U237.2 (DOUT), U238.4 (DIN)
unnamed: U238.2 (DOUT), U239.4 (DIN)
unnamed: U239.2 (DOUT), U240.4 (DIN)
unnamed: U240.2 (DOUT), U241.4 (DIN)
unnamed: U241.2 (DOUT), U242.4 (DIN)
unnamed: U242.2 (DOUT), U243.4 (DIN)
unnamed: U243.2 (DOUT), U244.4 (DIN)
unnamed: U244.2 (DOUT), U245.4 (DIN)
unnamed: U245.2 (DOUT), U246.4 (DIN)
unnamed: U246.2 (DOUT), U247.4 (DIN)
unnamed: U247.2 (DOUT), U248.4 (DIN)
unnamed: U248.2 (DOUT), U249.4 (DIN)
unnamed: U249.2 (DOUT), U250.4 (DIN)
unnamed: U251.2 (DOUT), U252.4 (DIN)
unnamed: U252.2 (DOUT), U253.4 (DIN)
unnamed: U253.2 (DOUT), U254.4 (DIN)
unnamed: U254.2 (DOUT), U255.4 (DIN)
unnamed: U255.2 (DOUT), U256.4 (DIN)
unnamed: U256.2 (DOUT), U257.4 (DIN)
unnamed: U257.2 (DOUT), U258.4 (DIN)
unnamed: U258.2 (DOUT), U259.4 (DIN)
unnamed: U259.2 (DOUT), U260.4 (DIN)
unnamed: U260.2 (DOUT), U261.4 (DIN)
unnamed: U261.2 (DOUT), U262.4 (DIN)
unnamed: U262.2 (DOUT), U263.4 (DIN)
unnamed: U263.2 (DOUT), U264.4 (DIN)
unnamed: U264.2 (DOUT), U265.4 (DIN)
unnamed: U265.2 (DOUT), U266.4 (DIN)
unnamed: U266.2 (DOUT), U267.4 (DIN)
unnamed: U267.2 (DOUT), U268.4 (DIN)
unnamed: U268.2 (DOUT), U269.4 (DIN)
unnamed: U269.2 (DOUT), U270.4 (DIN)
unnamed: U270.2 (DOUT), U271.4 (DIN)
unnamed: U271.2 (DOUT), U272.4 (DIN)
unnamed: U272.2 (DOUT), U273.4 (DIN)
unnamed: U273.2 (DOUT), U274.4 (DIN)
unnamed: U274.2 (DOUT), U275.4 (DIN)
unnamed: U276.2 (DOUT), U277.4 (DIN)
unnamed: U277.2 (DOUT), U278.4 (DIN)
unnamed: U278.2 (DOUT), U279.4 (DIN)
unnamed: U279.2 (DOUT), U280.4 (DIN)
unnamed: U280.2 (DOUT), U281.4 (DIN)
unnamed: U281.2 (DOUT), U282.4 (DIN)
unnamed: U282.2 (DOUT), U283.4 (DIN)
unnamed: U283.2 (DOUT), U284.4 (DIN)
unnamed: U284.2 (DOUT), U285.4 (DIN)
unnamed: U285.2 (DOUT), U286.4 (DIN)
unnamed: U286.2 (DOUT), U287.4 (DIN)
unnamed: U287.2 (DOUT), U288.4 (DIN)
unnamed: U288.2 (DOUT), U289.4 (DIN)
unnamed: U289.2 (DOUT), U290.4 (DIN)
unnamed: U290.2 (DOUT), U291.4 (DIN)
unnamed: U291.2 (DOUT), U292.4 (DIN)
unnamed: U292.2 (DOUT), U293.4 (DIN)
unnamed: U293.2 (DOUT), U294.4 (DIN)
unnamed: U294.2 (DOUT), U295.4 (DIN)
unnamed: U295.2 (DOUT), U296.4 (DIN)
unnamed: U296.2 (DOUT), U297.4 (DIN)
unnamed: U297.2 (DOUT), U298.4 (DIN)
unnamed: U298.2 (DOUT), U299.4 (DIN)
unnamed: U299.2 (DOUT), U300.4 (DIN)
unnamed: U301.2 (DOUT), U302.4 (DIN)
unnamed: U302.2 (DOUT), U303.4 (DIN)
unnamed: U303.2 (DOUT), U304.4 (DIN)
unnamed: U304.2 (DOUT), U305.4 (DIN)
unnamed: U305.2 (DOUT), U306.4 (DIN)
unnamed: U306.2 (DOUT), U307.4 (DIN)
unnamed: U307.2 (DOUT), U308.4 (DIN)
unnamed: U308.2 (DOUT), U309.4 (DIN)
unnamed: U309.2 (DOUT), U310.4 (DIN)
unnamed: U310.2 (DOUT), U311.4 (DIN)
unnamed: U311.2 (DOUT), U312.4 (DIN)
unnamed: U312.2 (DOUT), U313.4 (DIN)
unnamed: U313.2 (DOUT), U314.4 (DIN)
unnamed: U314.2 (DOUT), U315.4 (DIN)
unnamed: U315.2 (DOUT), U316.4 (DIN)
unnamed: U316.2 (DOUT), U317.4 (DIN)
unnamed: U317.2 (DOUT), U318.4 (DIN)
unnamed: U318.2 (DOUT), U319.4 (DIN)
unnamed: U319.2 (DOUT), U320.4 (DIN)
unnamed: U320.2 (DOUT), U321.4 (DIN)
unnamed: U321.2 (DOUT), U322.4 (DIN)
unnamed: U322.2 (DOUT), U323.4 (DIN)
unnamed: U323.2 (DOUT), U324.4 (DIN)
unnamed: U324.2 (DOUT), U325.4 (DIN)
unnamed: U326.2 (DOUT), U327.4 (DIN)
unnamed: U327.2 (DOUT), U328.4 (DIN)
unnamed: U328.2 (DOUT), U329.4 (DIN)
unnamed: U329.2 (DOUT), U330.4 (DIN)
unnamed: U330.2 (DOUT), U331.4 (DIN)
unnamed: U331.2 (DOUT), U332.4 (DIN)
unnamed: U332.2 (DOUT), U333.4 (DIN)
unnamed: U333.2 (DOUT), U334.4 (DIN)
unnamed: U334.2 (DOUT), U335.4 (DIN)
unnamed: U335.2 (DOUT), U336.4 (DIN)
unnamed: U336.2 (DOUT), U337.4 (DIN)
unnamed: U337.2 (DOUT), U338.4 (DIN)
unnamed: U338.2 (DOUT), U339.4 (DIN)
unnamed: U339.2 (DOUT), U340.4 (DIN)
unnamed: U340.2 (DOUT), U341.4 (DIN)
unnamed: U341.2 (DOUT), U342.4 (DIN)
unnamed: U342.2 (DOUT), U343.4 (DIN)
unnamed: U343.2 (DOUT), U344.4 (DIN)
unnamed: U344.2 (DOUT), U345.4 (DIN)
unnamed: U345.2 (DOUT), U346.4 (DIN)
unnamed: U346.2 (DOUT), U347.4 (DIN)
unnamed: U347.2 (DOUT), U348.4 (DIN)
unnamed: U348.2 (DOUT), U349.4 (DIN)
unnamed: U349.2 (DOUT), U350.4 (DIN)
unnamed: U351.2 (DOUT), U352.4 (DIN)
unnamed: U352.2 (DOUT), U353.4 (DIN)
unnamed: U353.2 (DOUT), U354.4 (DIN)
unnamed: U354.2 (DOUT), U355.4 (DIN)
unnamed: U355.2 (DOUT), U356.4 (DIN)
unnamed: U356.2 (DOUT), U357.4 (DIN)
unnamed: U357.2 (DOUT), U358.4 (DIN)
unnamed: U358.2 (DOUT), U359.4 (DIN)
unnamed: U359.2 (DOUT), U360.4 (DIN)
unnamed: U360.2 (DOUT), U361.4 (DIN)
unnamed: U361.2 (DOUT), U362.4 (DIN)
unnamed: U362.2 (DOUT), U363.4 (DIN)
unnamed: U363.2 (DOUT), U364.4 (DIN)
unnamed: U364.2 (DOUT), U365.4 (DIN)
unnamed: U365.2 (DOUT), U366.4 (DIN)
unnamed: U366.2 (DOUT), U367.4 (DIN)
unnamed: U367.2 (DOUT), U368.4 (DIN)
unnamed: U368.2 (DOUT), U369.4 (DIN)
unnamed: U369.2 (DOUT), U370.4 (DIN)
unnamed: U370.2 (DOUT), U371.4 (DIN)
unnamed: U371.2 (DOUT), U372.4 (DIN)
unnamed: U372.2 (DOUT), U373.4 (DIN)
unnamed: U373.2 (DOUT), U374.4 (DIN)
unnamed: U374.2 (DOUT), U375.4 (DIN)
unnamed: U376.2 (DOUT), U377.4 (DIN)
unnamed: U377.2 (DOUT), U378.4 (DIN)
unnamed: U378.2 (DOUT), U379.4 (DIN)
unnamed: U379.2 (DOUT), U380.4 (DIN)
unnamed: U380.2 (DOUT), U381.4 (DIN)
unnamed: U381.2 (DOUT), U382.4 (DIN)
unnamed: U382.2 (DOUT), U383.4 (DIN)
unnamed: U383.2 (DOUT), U384.4 (DIN)
unnamed: U384.2 (DOUT), U385.4 (DIN)
unnamed: U385.2 (DOUT), U386.4 (DIN)
unnamed: U386.2 (DOUT), U387.4 (DIN)
unnamed: U387.2 (DOUT), U388.4 (DIN)
unnamed: U388.2 (DOUT), U389.4 (DIN)
unnamed: U389.2 (DOUT), U390.4 (DIN)
unnamed: U390.2 (DOUT), U391.4 (DIN)
unnamed: U391.2 (DOUT), U392.4 (DIN)
unnamed: U392.2 (DOUT), U393.4 (DIN)
unnamed: U393.2 (DOUT), U394.4 (DIN)
unnamed: U394.2 (DOUT), U395.4 (DIN)
unnamed: U395.2 (DOUT), U396.4 (DIN)
unnamed: U396.2 (DOUT), U397.4 (DIN)
unnamed: U397.2 (DOUT), U398.4 (DIN)
unnamed: U398.2 (DOUT), U399.4 (DIN)
unnamed: U399.2 (DOUT), U400.4 (DIN)
unnamed: U401.2 (DOUT), U402.4 (DIN)
unnamed: U402.2 (DOUT), U403.4 (DIN)
unnamed: U403.2 (DOUT), U404.4 (DIN)
unnamed: U404.2 (DOUT), U405.4 (DIN)
unnamed: U405.2 (DOUT), U406.4 (DIN)
unnamed: U406.2 (DOUT), U407.4 (DIN)
unnamed: U407.2 (DOUT), U408.4 (DIN)
unnamed: U408.2 (DOUT), U409.4 (DIN)
unnamed: U409.2 (DOUT), U410.4 (DIN)
unnamed: U410.2 (DOUT), U411.4 (DIN)
unnamed: U411.2 (DOUT), U412.4 (DIN)
unnamed: U412.2 (DOUT), U413.4 (DIN)
unnamed: U413.2 (DOUT), U414.4 (DIN)
unnamed: U414.2 (DOUT), U415.4 (DIN)
unnamed: U415.2 (DOUT), U416.4 (DIN)
unnamed: U416.2 (DOUT), U417.4 (DIN)
unnamed: U417.2 (DOUT), U418.4 (DIN)
unnamed: U418.2 (DOUT), U419.4 (DIN)
unnamed: U419.2 (DOUT), U420.4 (DIN)
unnamed: U420.2 (DOUT), U421.4 (DIN)
unnamed: U421.2 (DOUT), U422.4 (DIN)
unnamed: U422.2 (DOUT), U423.4 (DIN)
unnamed: U423.2 (DOUT), U424.4 (DIN)
unnamed: U424.2 (DOUT), U425.4 (DIN)
unnamed: U426.2 (DOUT), U427.4 (DIN)
unnamed: U427.2 (DOUT), U428.4 (DIN)
unnamed: U428.2 (DOUT), U429.4 (DIN)
unnamed: U429.2 (DOUT), U430.4 (DIN)
unnamed: U430.2 (DOUT), U431.4 (DIN)
unnamed: U431.2 (DOUT), U432.4 (DIN)
unnamed: U432.2 (DOUT), U433.4 (DIN)
unnamed: U433.2 (DOUT), U434.4 (DIN)
unnamed: U434.2 (DOUT), U435.4 (DIN)
unnamed: U435.2 (DOUT), U436.4 (DIN)
unnamed: U436.2 (DOUT), U437.4 (DIN)
unnamed: U437.2 (DOUT), U438.4 (DIN)
unnamed: U438.2 (DOUT), U439.4 (DIN)
unnamed: U439.2 (DOUT), U440.4 (DIN)
unnamed: U440.2 (DOUT), U441.4 (DIN)
unnamed: U441.2 (DOUT), U442.4 (DIN)
unnamed: U442.2 (DOUT), U443.4 (DIN)
unnamed: U443.2 (DOUT), U444.4 (DIN)
unnamed: U444.2 (DOUT), U445.4 (DIN)
unnamed: U445.2 (DOUT), U446.4 (DIN)
unnamed: U446.2 (DOUT), U447.4 (DIN)
unnamed: U447.2 (DOUT), U448.4 (DIN)
unnamed: U448.2 (DOUT), U449.4 (DIN)
unnamed: U449.2 (DOUT), U450.4 (DIN)
unnamed: U451.2 (DOUT), U452.4 (DIN)
unnamed: U452.2 (DOUT), U453.4 (DIN)
unnamed: U453.2 (DOUT), U454.4 (DIN)
unnamed: U454.2 (DOUT), U455.4 (DIN)
unnamed: U455.2 (DOUT), U456.4 (DIN)
unnamed: U456.2 (DOUT), U457.4 (DIN)
unnamed: U457.2 (DOUT), U458.4 (DIN)
unnamed: U458.2 (DOUT), U459.4 (DIN)
unnamed: U459.2 (DOUT), U460.4 (DIN)
unnamed: U460.2 (DOUT), U461.4 (DIN)
unnamed: U461.2 (DOUT), U462.4 (DIN)
unnamed: U462.2 (DOUT), U463.4 (DIN)
unnamed: U463.2 (DOUT), U464.4 (DIN)
unnamed: U464.2 (DOUT), U465.4 (DIN)
unnamed: U465.2 (DOUT), U466.4 (DIN)
unnamed: U466.2 (DOUT), U467.4 (DIN)
unnamed: U467.2 (DOUT), U468.4 (DIN)
unnamed: U468.2 (DOUT), U469.4 (DIN)
unnamed: U469.2 (DOUT), U470.4 (DIN)
unnamed: U470.2 (DOUT), U471.4 (DIN)
unnamed: U471.2 (DOUT), U472.4 (DIN)
unnamed: U472.2 (DOUT), U473.4 (DIN)
unnamed: U473.2 (DOUT), U474.4 (DIN)
unnamed: U474.2 (DOUT), U475.4 (DIN)
unnamed: U476.2 (DOUT), U477.4 (DIN)
unnamed: U477.2 (DOUT), U478.4 (DIN)
unnamed: U478.2 (DOUT), U479.4 (DIN)
unnamed: U479.2 (DOUT), U480.4 (DIN)
unnamed: U480.2 (DOUT), U481.4 (DIN)
unnamed: U481.2 (DOUT), U482.4 (DIN)
unnamed: U482.2 (DOUT), U483.4 (DIN)
unnamed: U483.2 (DOUT), U484.4 (DIN)
unnamed: U484.2 (DOUT), U485.4 (DIN)
unnamed: U485.2 (DOUT), U486.4 (DIN)
unnamed: U486.2 (DOUT), U487.4 (DIN)
unnamed: U487.2 (DOUT), U488.4 (DIN)
unnamed: U488.2 (DOUT), U489.4 (DIN)
unnamed: U489.2 (DOUT), U490.4 (DIN)
unnamed: U490.2 (DOUT), U491.4 (DIN)
unnamed: U491.2 (DOUT), U492.4 (DIN)
unnamed: U492.2 (DOUT), U493.4 (DIN)
unnamed: U493.2 (DOUT), U494.4 (DIN)
unnamed: U494.2 (DOUT), U495.4 (DIN)
unnamed: U495.2 (DOUT), U496.4 (DIN)
unnamed: U496.2 (DOUT), U497.4 (DIN)
unnamed: U497.2 (DOUT), U498.4 (DIN)
unnamed: U498.2 (DOUT), U499.4 (DIN)
unnamed: U499.2 (DOUT), U500.4 (DIN)
unnamed: U501.2 (DOUT), U502.4 (DIN)
unnamed: U502.2 (DOUT), U503.4 (DIN)
unnamed: U503.2 (DOUT), U504.4 (DIN)
unnamed: U504.2 (DOUT), U505.4 (DIN)
unnamed: U505.2 (DOUT), U506.4 (DIN)
unnamed: U506.2 (DOUT), U507.4 (DIN)
unnamed: U507.2 (DOUT), U508.4 (DIN)
unnamed: U508.2 (DOUT), U509.4 (DIN)
unnamed: U509.2 (DOUT), U510.4 (DIN)
unnamed: U510.2 (DOUT), U511.4 (DIN)
unnamed: U511.2 (DOUT), U512.4 (DIN)
unnamed: U512.2 (DOUT), U513.4 (DIN)
unnamed: U513.2 (DOUT), U514.4 (DIN)
unnamed: U514.2 (DOUT), U515.4 (DIN)
unnamed: U515.2 (DOUT), U516.4 (DIN)
unnamed: U516.2 (DOUT), U517.4 (DIN)
unnamed: U517.2 (DOUT), U518.4 (DIN)
unnamed: U518.2 (DOUT), U519.4 (DIN)
unnamed: U519.2 (DOUT), U520.4 (DIN)
unnamed: U520.2 (DOUT), U521.4 (DIN)
unnamed: U521.2 (DOUT), U522.4 (DIN)
unnamed: U522.2 (DOUT), U523.4 (DIN)
unnamed: U523.2 (DOUT), U524.4 (DIN)
unnamed: U524.2 (DOUT), U525.4 (DIN)
unnamed: U526.2 (DOUT), U527.4 (DIN)
unnamed: U527.2 (DOUT), U528.4 (DIN)
unnamed: U528.2 (DOUT), U529.4 (DIN)
unnamed: U529.2 (DOUT), U530.4 (DIN)
unnamed: U530.2 (DOUT), U531.4 (DIN)
unnamed: U531.2 (DOUT), U532.4 (DIN)
unnamed: U532.2 (DOUT), U533.4 (DIN)
unnamed: U533.2 (DOUT), U534.4 (DIN)
unnamed: U534.2 (DOUT), U535.4 (DIN)
unnamed: U535.2 (DOUT), U536.4 (DIN)
unnamed: U536.2 (DOUT), U537.4 (DIN)
unnamed: U537.2 (DOUT), U538.4 (DIN)
unnamed: U538.2 (DOUT), U539.4 (DIN)
unnamed: U539.2 (DOUT), U540.4 (DIN)
unnamed: U540.2 (DOUT), U541.4 (DIN)
unnamed: U541.2 (DOUT), U542.4 (DIN)
unnamed: U542.2 (DOUT), U543.4 (DIN)
unnamed: U543.2 (DOUT), U544.4 (DIN)
unnamed: U544.2 (DOUT), U545.4 (DIN)
unnamed: U545.2 (DOUT), U546.4 (DIN)
unnamed: U546.2 (DOUT), U547.4 (DIN)
unnamed: U547.2 (DOUT), U548.4 (DIN)
unnamed: U548.2 (DOUT), U549.4 (DIN)
unnamed: U549.2 (DOUT), U550.4 (DIN)
unnamed: U551.2 (DOUT), U552.4 (DIN)
unnamed: U552.2 (DOUT), U553.4 (DIN)
unnamed: U553.2 (DOUT), U554.4 (DIN)
unnamed: U554.2 (DOUT), U555.4 (DIN)
unnamed: U555.2 (DOUT), U556.4 (DIN)
unnamed: U556.2 (DOUT), U557.4 (DIN)
unnamed: U557.2 (DOUT), U558.4 (DIN)
unnamed: U558.2 (DOUT), U559.4 (DIN)
unnamed: U559.2 (DOUT), U560.4 (DIN)
unnamed: U560.2 (DOUT), U561.4 (DIN)
unnamed: U561.2 (DOUT), U562.4 (DIN)
unnamed: U562.2 (DOUT), U563.4 (DIN)
unnamed: U563.2 (DOUT), U564.4 (DIN)
unnamed: U564.2 (DOUT), U565.4 (DIN)
unnamed: U565.2 (DOUT), U566.4 (DIN)
unnamed: U566.2 (DOUT), U567.4 (DIN)
unnamed: U567.2 (DOUT), U568.4 (DIN)
unnamed: U568.2 (DOUT), U569.4 (DIN)
unnamed: U569.2 (DOUT), U570.4 (DIN)
unnamed: U570.2 (DOUT), U571.4 (DIN)
unnamed: U571.2 (DOUT), U572.4 (DIN)
unnamed: U572.2 (DOUT), U573.4 (DIN)
unnamed: U573.2 (DOUT), U574.4 (DIN)
unnamed: U574.2 (DOUT), U575.4 (DIN)
unnamed: U576.2 (DOUT), U577.4 (DIN)
unnamed: U577.2 (DOUT), U578.4 (DIN)
unnamed: U578.2 (DOUT), U579.4 (DIN)
unnamed: U579.2 (DOUT), U580.4 (DIN)
unnamed: U580.2 (DOUT), U581.4 (DIN)
unnamed: U581.2 (DOUT), U582.4 (DIN)
unnamed: U582.2 (DOUT), U583.4 (DIN)
unnamed: U583.2 (DOUT), U584.4 (DIN)
unnamed: U584.2 (DOUT), U585.4 (DIN)
unnamed: U585.2 (DOUT), U586.4 (DIN)
unnamed: U586.2 (DOUT), U587.4 (DIN)
unnamed: U587.2 (DOUT), U588.4 (DIN)
unnamed: U588.2 (DOUT), U589.4 (DIN)
unnamed: U589.2 (DOUT), U590.4 (DIN)
unnamed: U590.2 (DOUT), U591.4 (DIN)
unnamed: U591.2 (DOUT), U592.4 (DIN)
unnamed: U592.2 (DOUT), U593.4 (DIN)
unnamed: U593.2 (DOUT), U594.4 (DIN)
unnamed: U594.2 (DOUT), U595.4 (DIN)
unnamed: U595.2 (DOUT), U596.4 (DIN)
unnamed: U596.2 (DOUT), U597.4 (DIN)
unnamed: U597.2 (DOUT), U598.4 (DIN)
unnamed: U598.2 (DOUT), U599.4 (DIN)
unnamed: U599.2 (DOUT), U600.4 (DIN)

Notes on the sheet:
Not Used
Mounting Holes
Main Board Input
600 WS2812B LEDs
